Lucassifoni/hyperbolic-200mm-f3.5-/base mirror (ouch)/_MG_7760.JPG

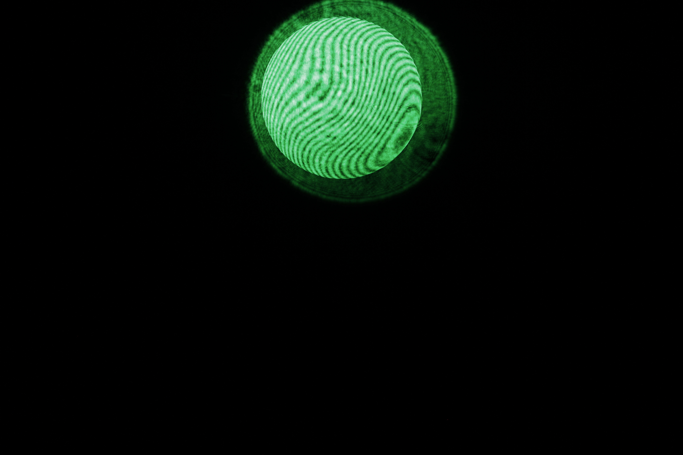
base mirror (ouch)/_MG_7760.JPG
