Lucassifoni/hyperbolic-200mm-f3.5-/base mirror (ouch)/Annotation 2022-02-02 160136.jpg

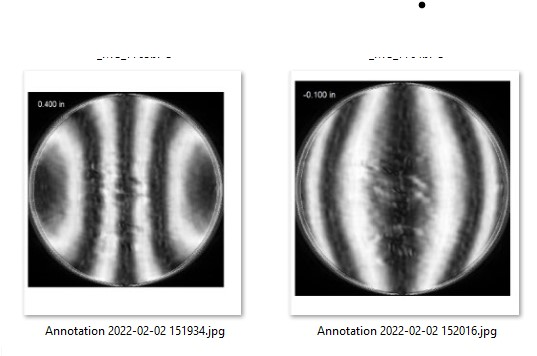
base mirror (ouch)/Annotation 2022-02-02 160136.jpg
