Lucassifoni/hyperbolic-200mm-f3.5-/base mirror (ouch)/fd45.jpg

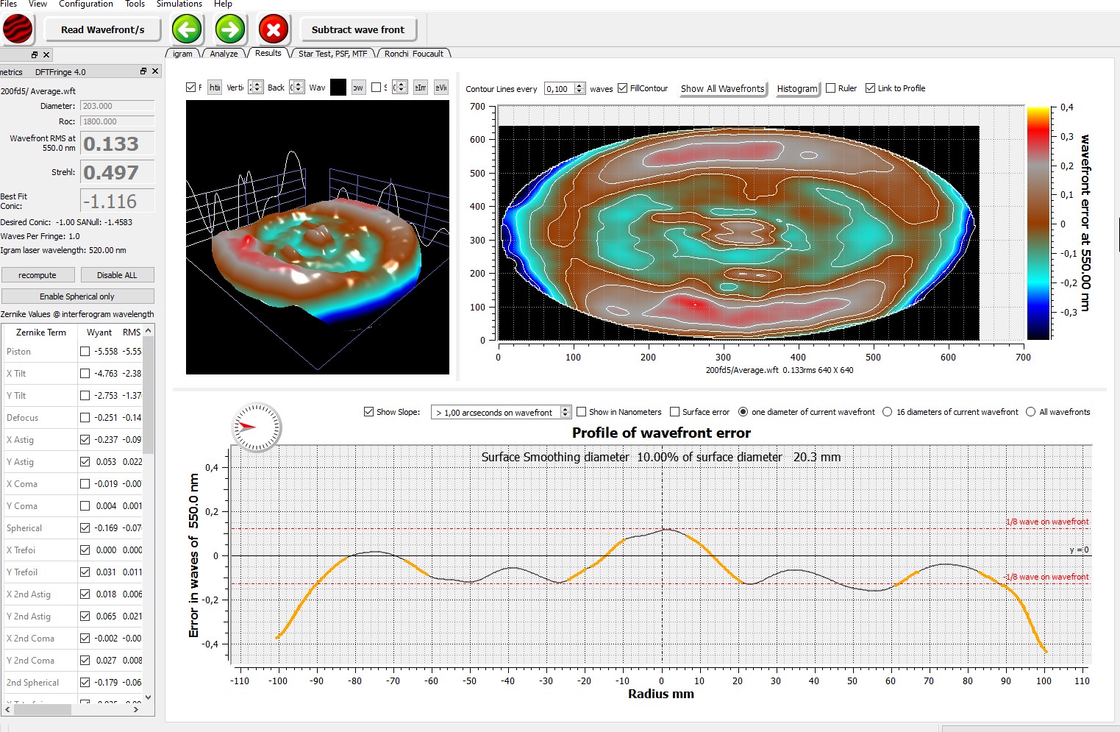
base mirror (ouch)/fd45.jpg
