Lucassifoni/hyperbolic-200mm-f3.5-/base mirror (ouch)/MPCC post-3008-0-78724300-1481155795.jpg

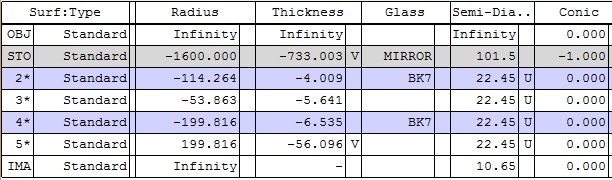
base mirror (ouch)/MPCC post-3008-0-78724300-1481155795.jpg
