Lucassifoni/hyperbolic-200mm-f3.5-/base mirror (ouch)/source/_MG_7740.JPG

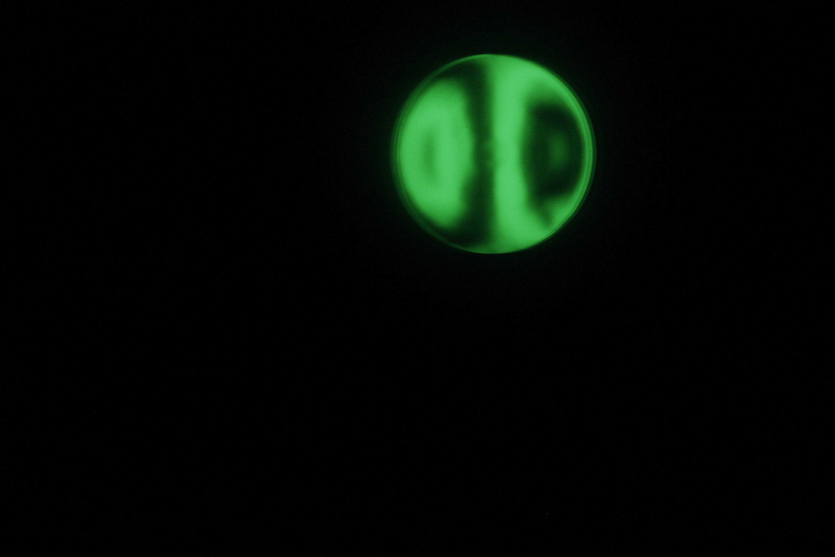
base mirror (ouch)/source/_MG_7740.JPG
