Lucassifoni/hyperbolic-200mm-f3.5-/base mirror (ouch)/source/_MG_7748.JPG

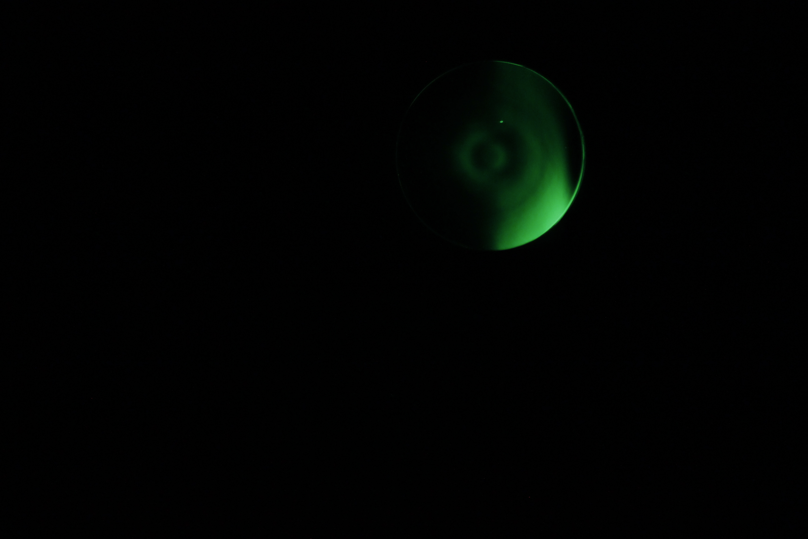
base mirror (ouch)/source/_MG_7748.JPG
