Lucassifoni/hyperbolic-200mm-f3.5-/figuring/session 0/0_sphere.jpeg

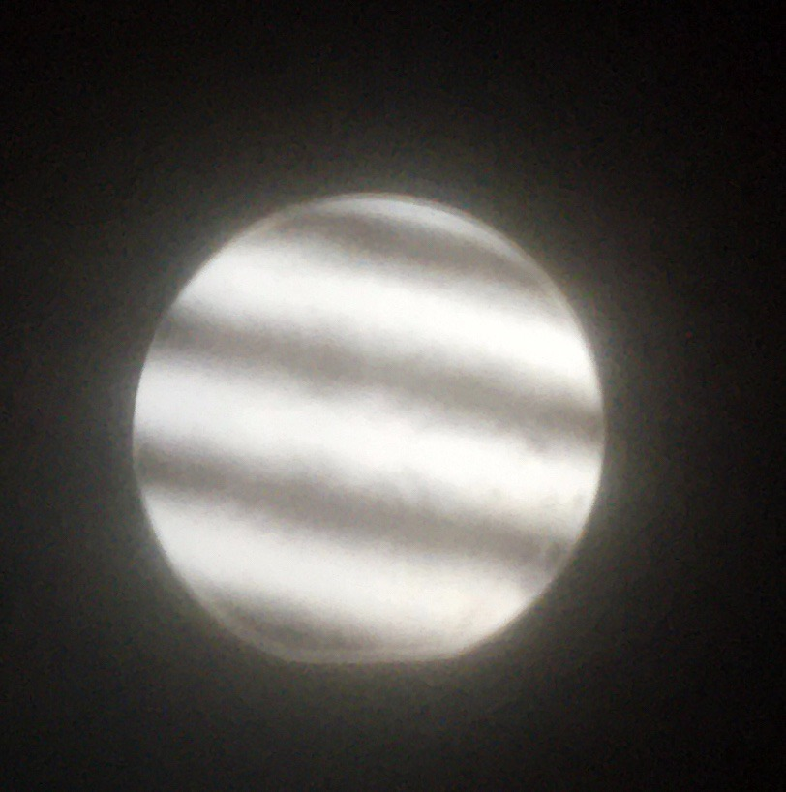
figuring/session 0/0_sphere.jpeg
