Lucassifoni/hyperbolic-200mm-f3.5-/figuring/session 1/1_outside.jpeg

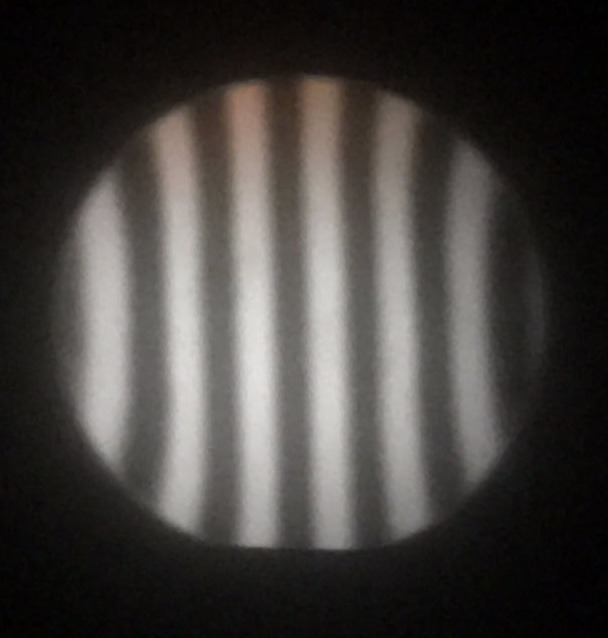
figuring/session 1/1_outside.jpeg
