Lucassifoni/hyperbolic-200mm-f3.5-/figuring/session 2/2_inside.jpeg

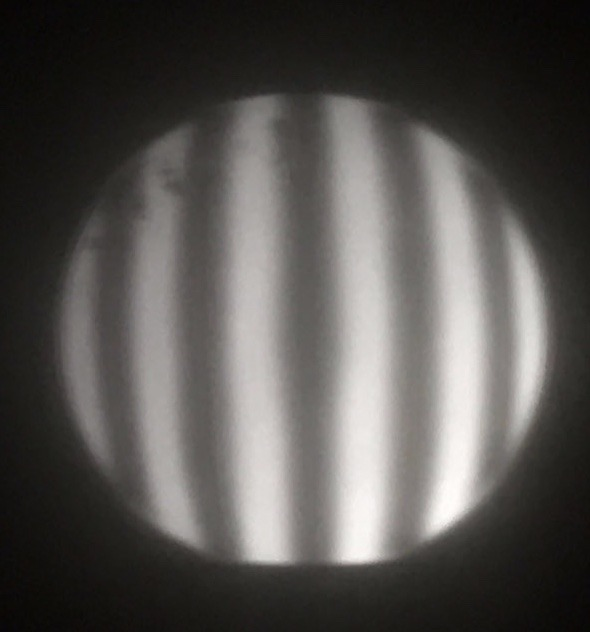
figuring/session 2/2_inside.jpeg
