Lucassifoni/hyperbolic-200mm-f3.5-/figuring/session 3/3_inside.jpeg

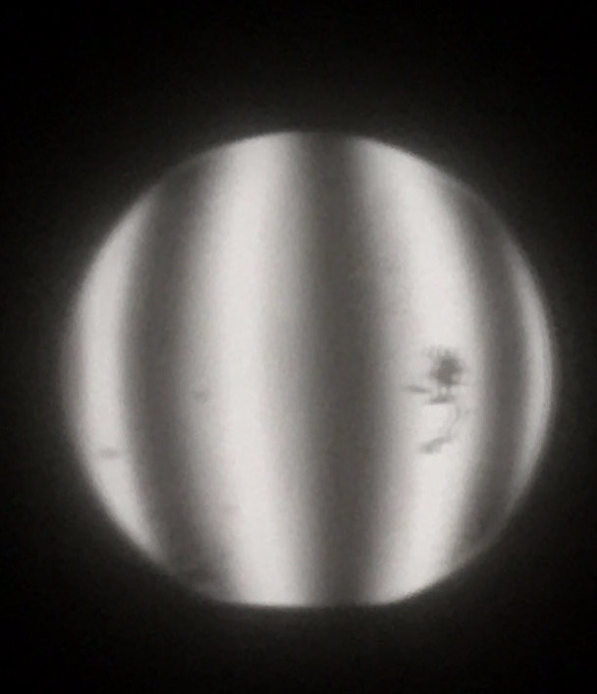
figuring/session 3/3_inside.jpeg
