Lucassifoni/hyperbolic-200mm-f3.5-/figuring/session 6/Capture.jpg

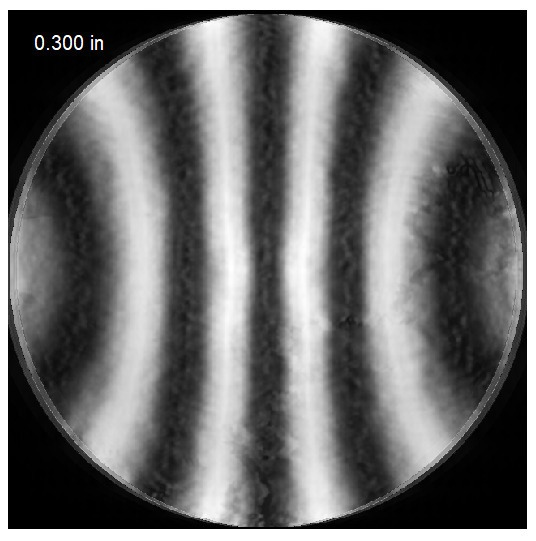
figuring/session 6/Capture.jpg
