Lucassifoni/hyperbolic-200mm-f3.5-/figuring/session 6/igrams/_MG_7814.JPG

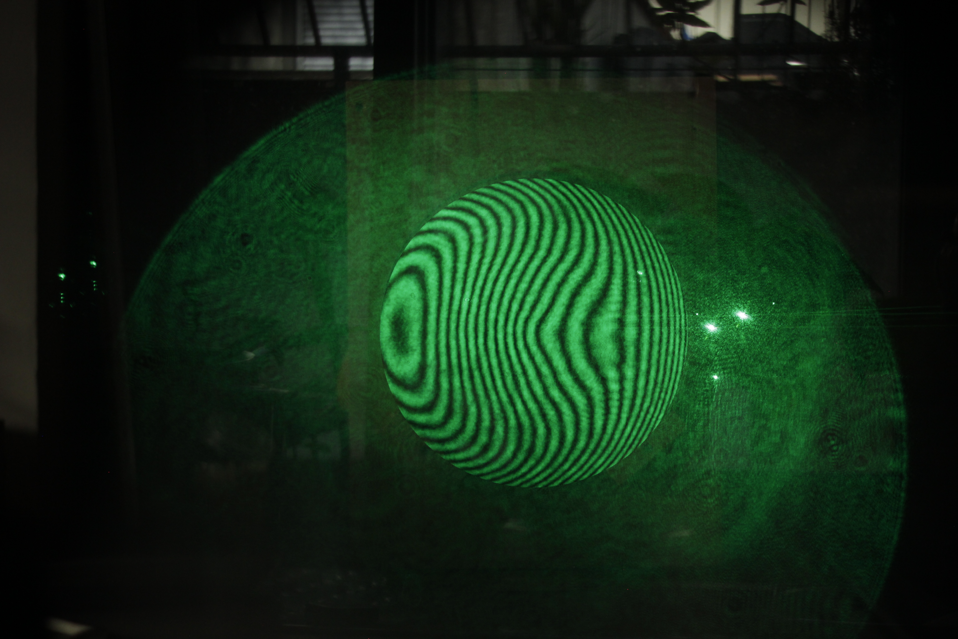
figuring/session 6/igrams/_MG_7814.JPG
