Lucassifoni/hyperbolic-200mm-f3.5-/figuring/session 7/lap.jpeg

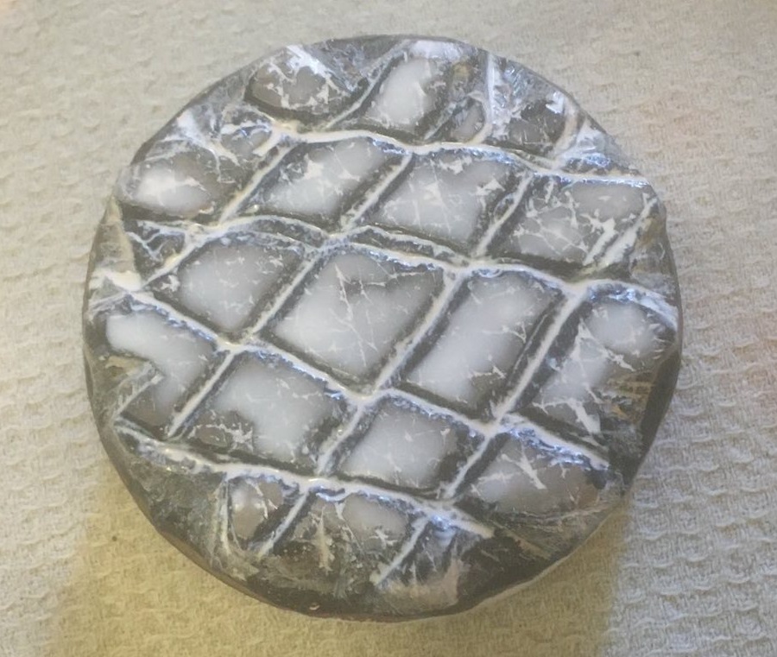
figuring/session 7/lap.jpeg
