Lucassifoni/hyperbolic-200mm-f3.5-/figuring/session 7/outside.jpeg

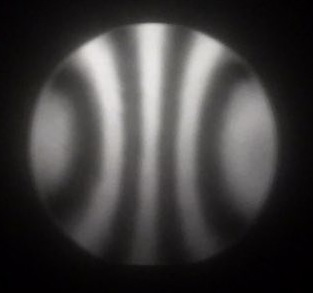
figuring/session 7/outside.jpeg
