Lucassifoni/hyperbolic-200mm-f3.5-/figuring/session 8/_MG_7846.JPG

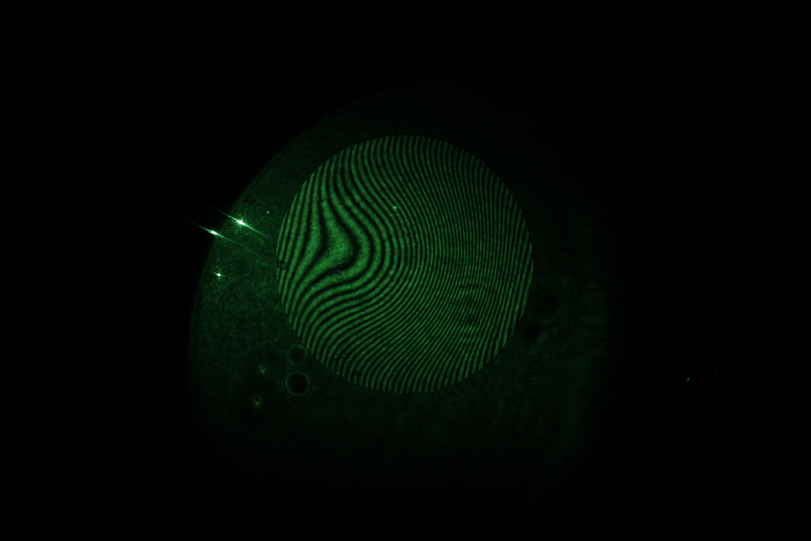
figuring/session 8/_MG_7846.JPG
