Lucassifoni/hyperbolic-200mm-f3.5-/figuring/session 8/_MG_7848.JPG

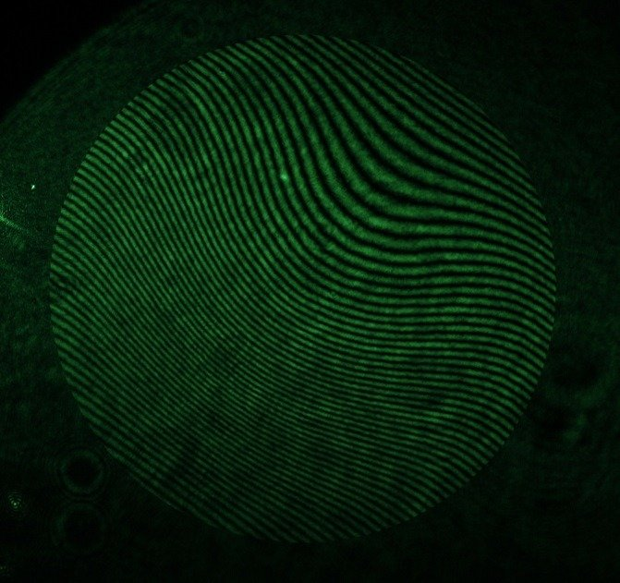
figuring/session 8/_MG_7848.JPG
