Lucassifoni/hyperbolic-200mm-f3.5-/figuring/session 8/Capture.JPG

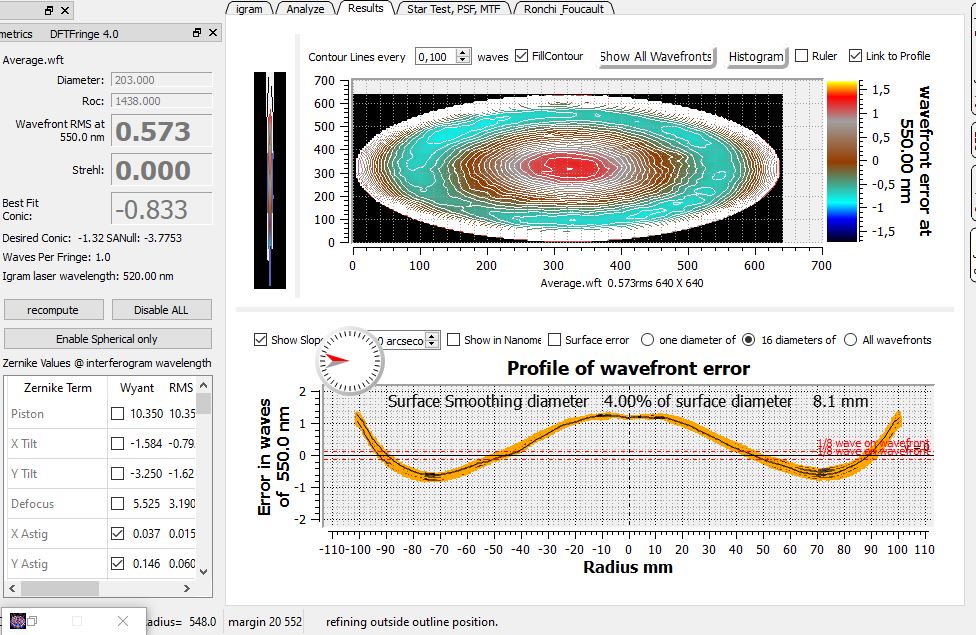
figuring/session 8/Capture.JPG
