Lucassifoni/hyperbolic-200mm-f3.5-/figuring/session 9/_MG_7857.JPG

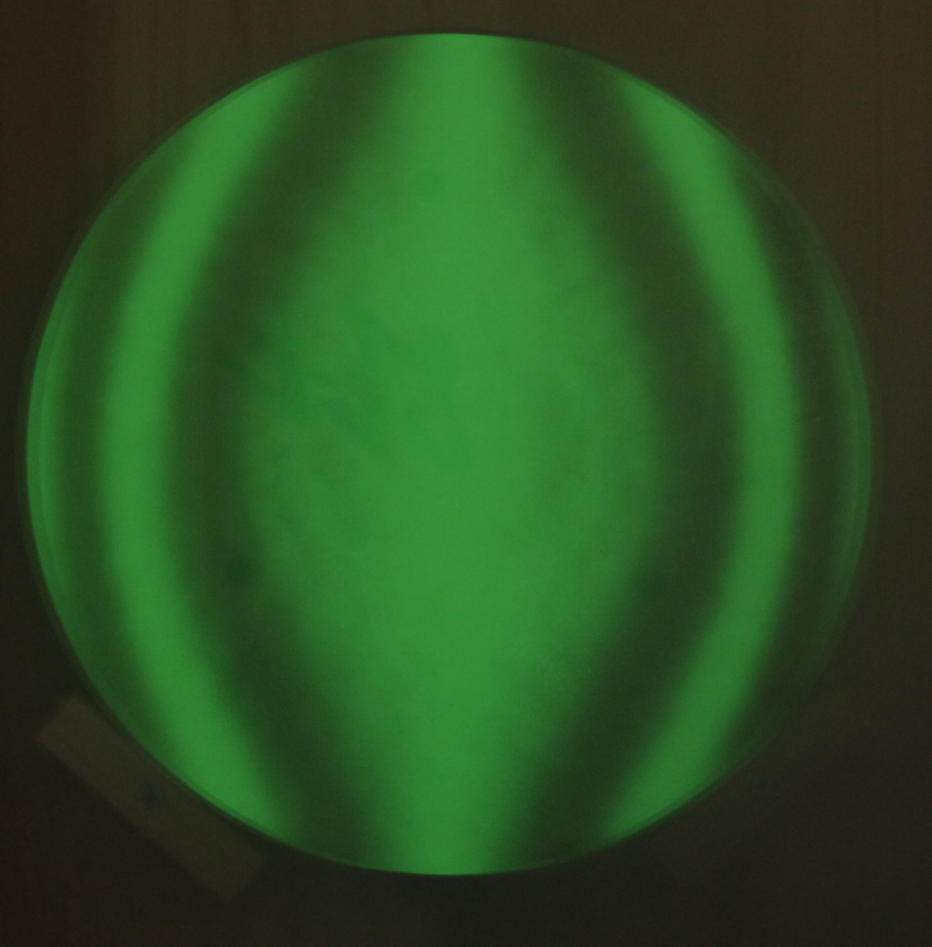
figuring/session 9/_MG_7857.JPG
