Lucassifoni/hyperbolic-200mm-f3.5-/figuring/session 11/_MG_7869.JPG

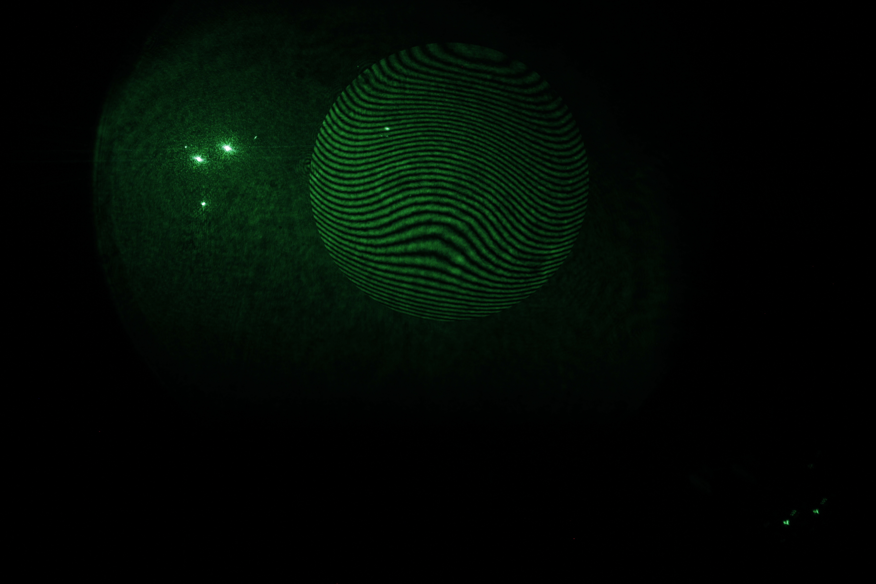
figuring/session 11/_MG_7869.JPG
