Lucassifoni/hyperbolic-200mm-f3.5-/figuring/session 11/_MG_7881.JPG

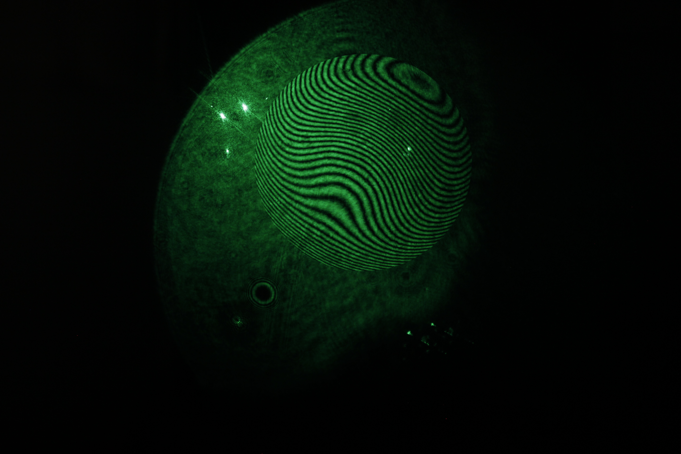
figuring/session 11/_MG_7881.JPG
