Lucassifoni/hyperbolic-200mm-f3.5-/figuring/session 12/_MG_7891.JPG

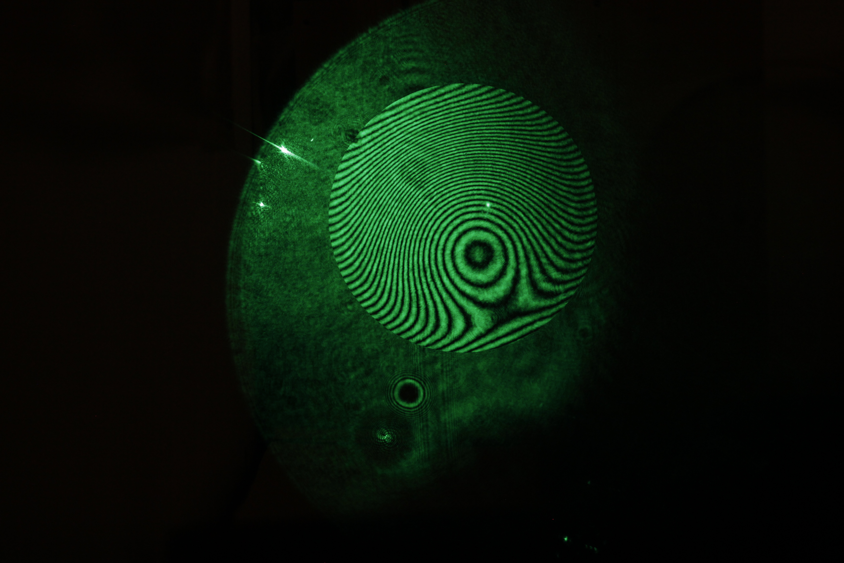
figuring/session 12/_MG_7891.JPG
