Lucassifoni/hyperbolic-200mm-f3.5-/figuring/session 12/_MG_7892.JPG

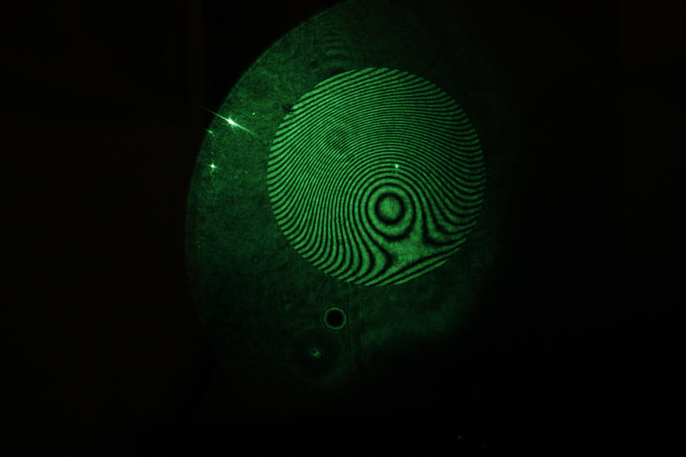
figuring/session 12/_MG_7892.JPG
