Lucassifoni/hyperbolic-200mm-f3.5-/figuring/session 12/Capture.JPG

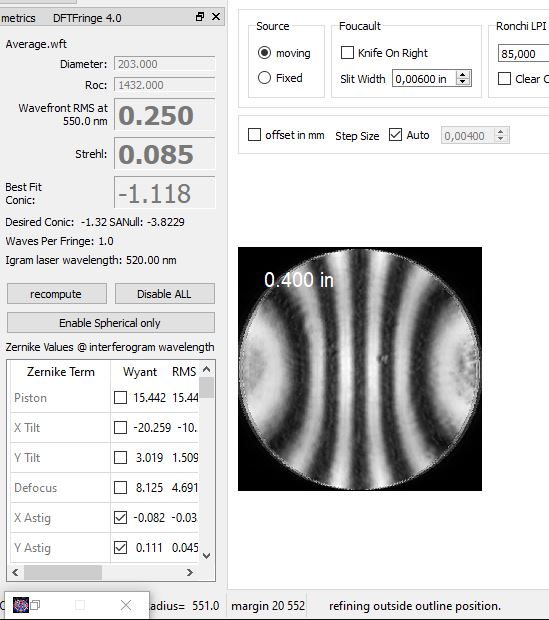
figuring/session 12/Capture.JPG
