Lucassifoni/hyperbolic-200mm-f3.5-/figuring/session 14/_MG_7916.JPG

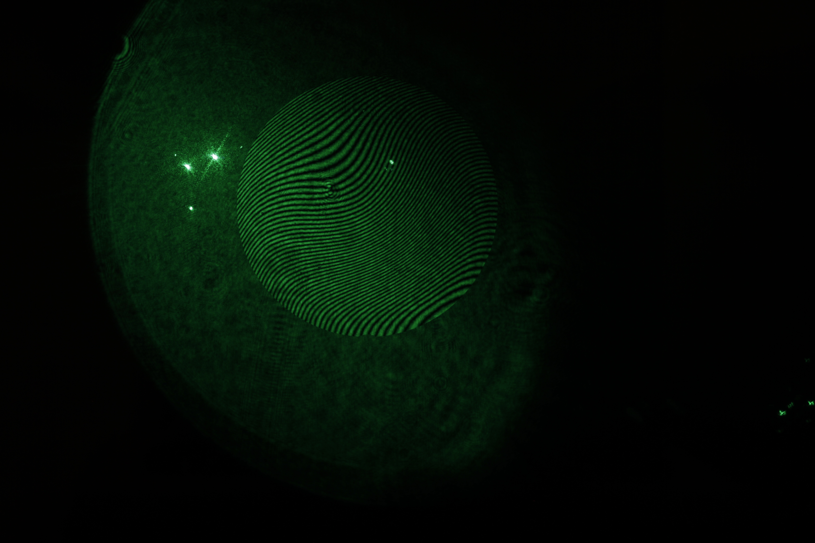
figuring/session 14/_MG_7916.JPG
