Lucassifoni/hyperbolic-200mm-f3.5-/figuring/session 14/_MG_7924.JPG

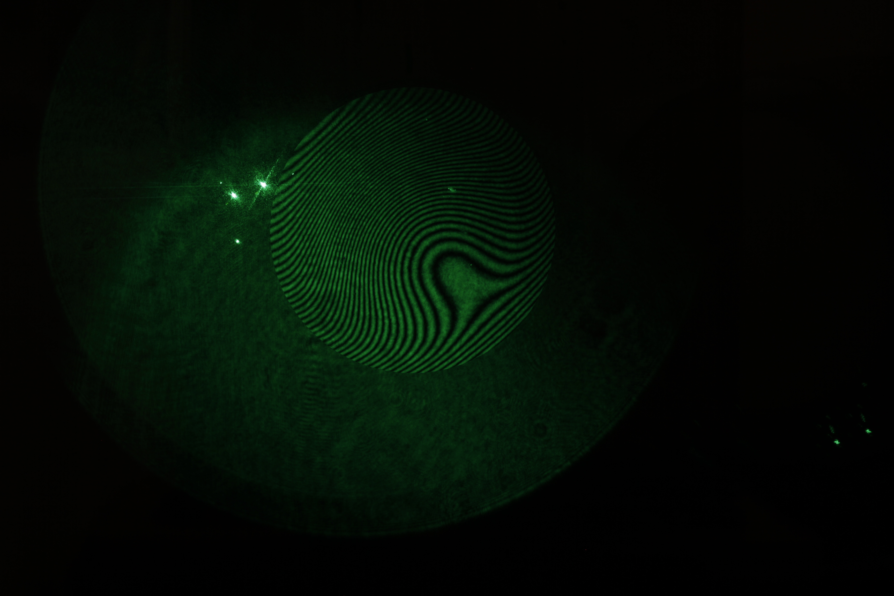
figuring/session 14/_MG_7924.JPG
