Lucassifoni/hyperbolic-200mm-f3.5-/figuring/session 14/Capture.JPG

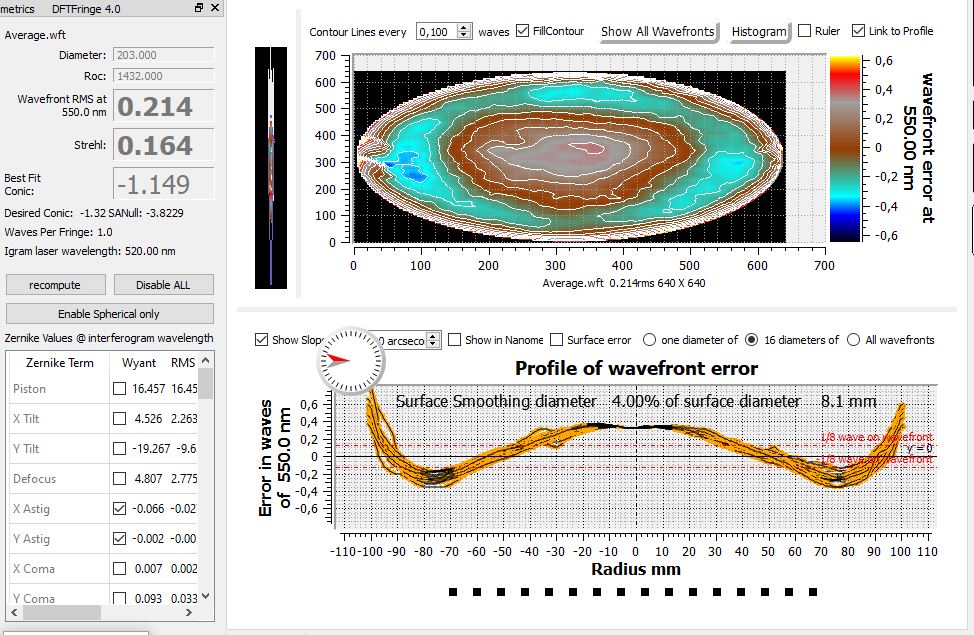
figuring/session 14/Capture.JPG
