Lucassifoni/hyperbolic-200mm-f3.5-/figuring/session 15/_MG_7925.JPG

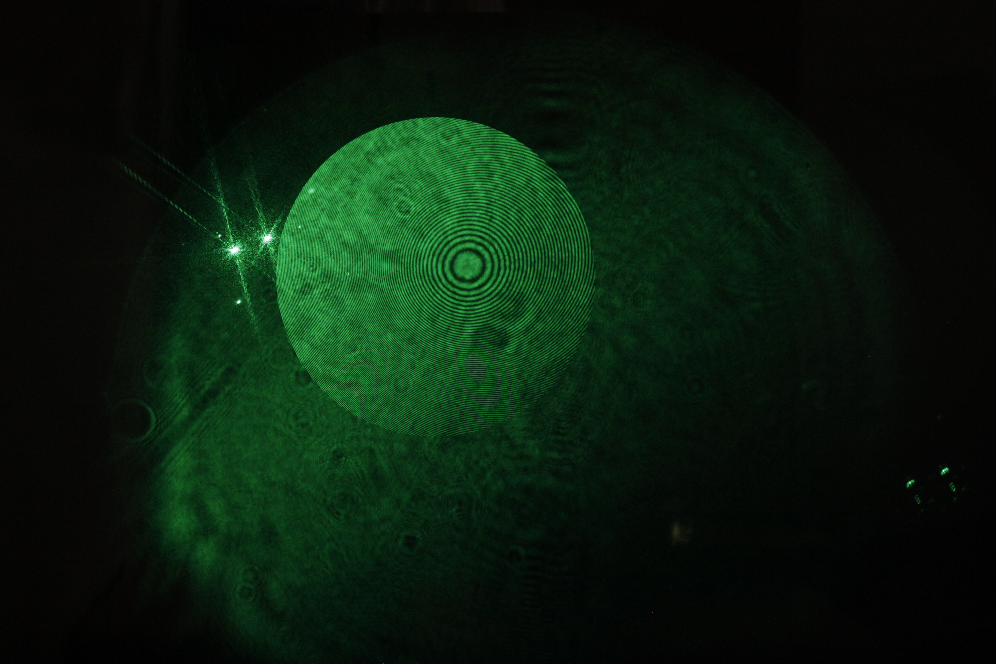
figuring/session 15/_MG_7925.JPG
