Lucassifoni/hyperbolic-200mm-f3.5-/figuring/session 15/_MG_7926.JPG

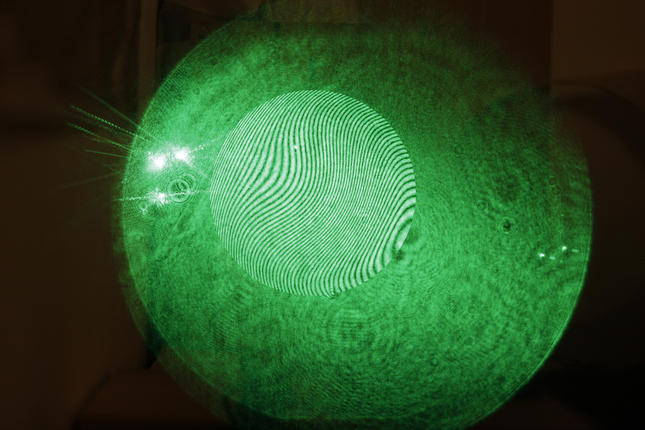
figuring/session 15/_MG_7926.JPG
