Lucassifoni/hyperbolic-200mm-f3.5-/figuring/session 15/Capture.JPG

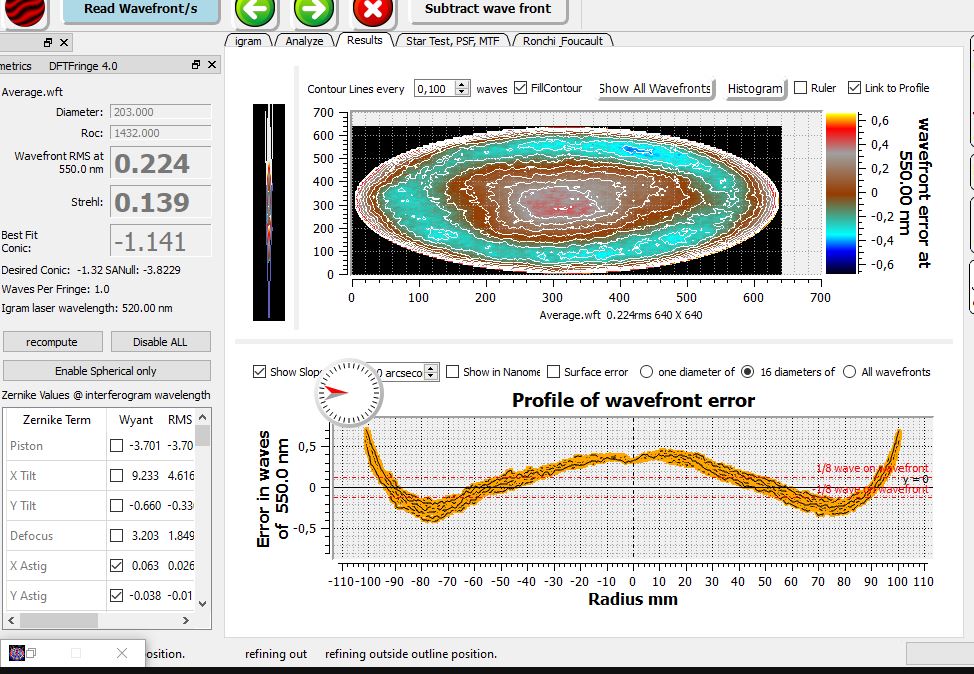
figuring/session 15/Capture.JPG
