Lucassifoni/hyperbolic-200mm-f3.5-/figuring/session 16/_MG_7944.JPG

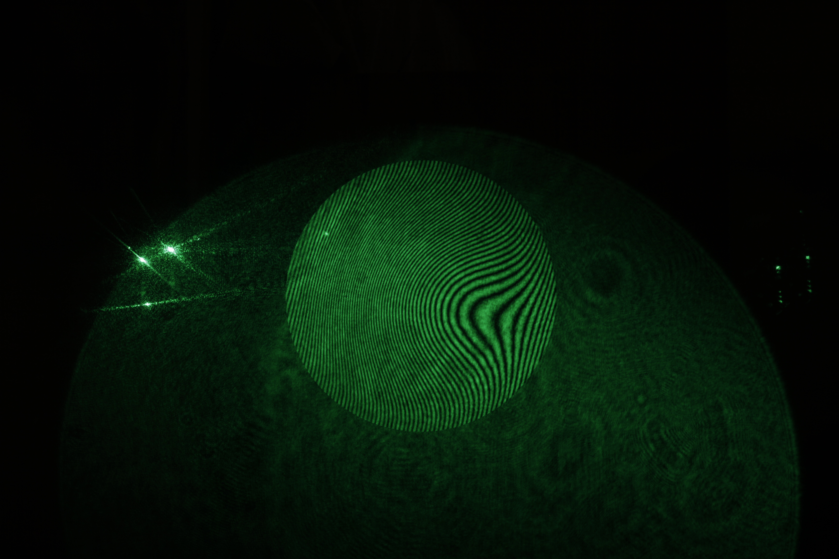
figuring/session 16/_MG_7944.JPG
