Lucassifoni/hyperbolic-200mm-f3.5-/figuring/session 16/unknown.png

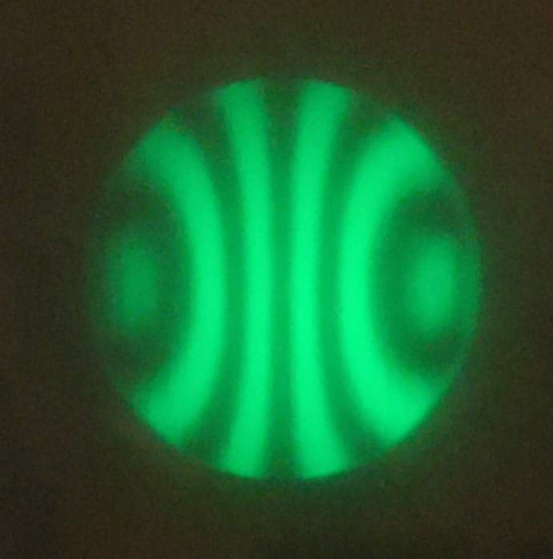
figuring/session 16/unknown.png
