Lucassifoni/hyperbolic-200mm-f3.5-/figuring/session 17/_MG_7948.JPG

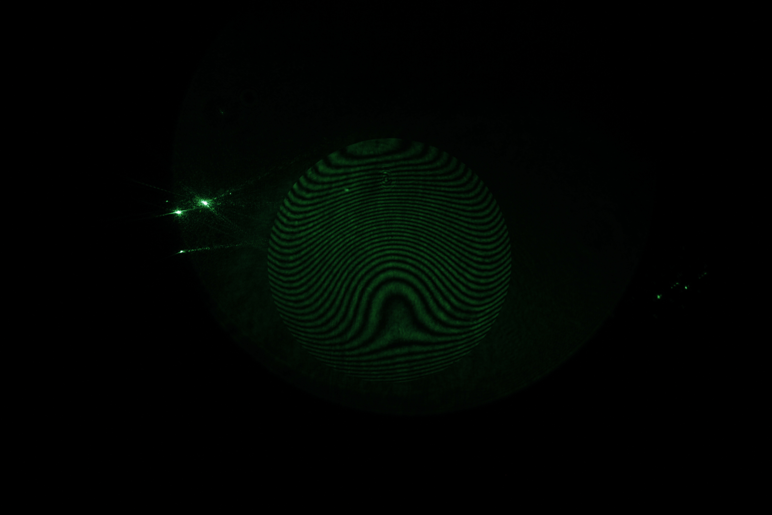
figuring/session 17/_MG_7948.JPG
