Lucassifoni/hyperbolic-200mm-f3.5-/figuring/session 17/CaptureSession17.PNG

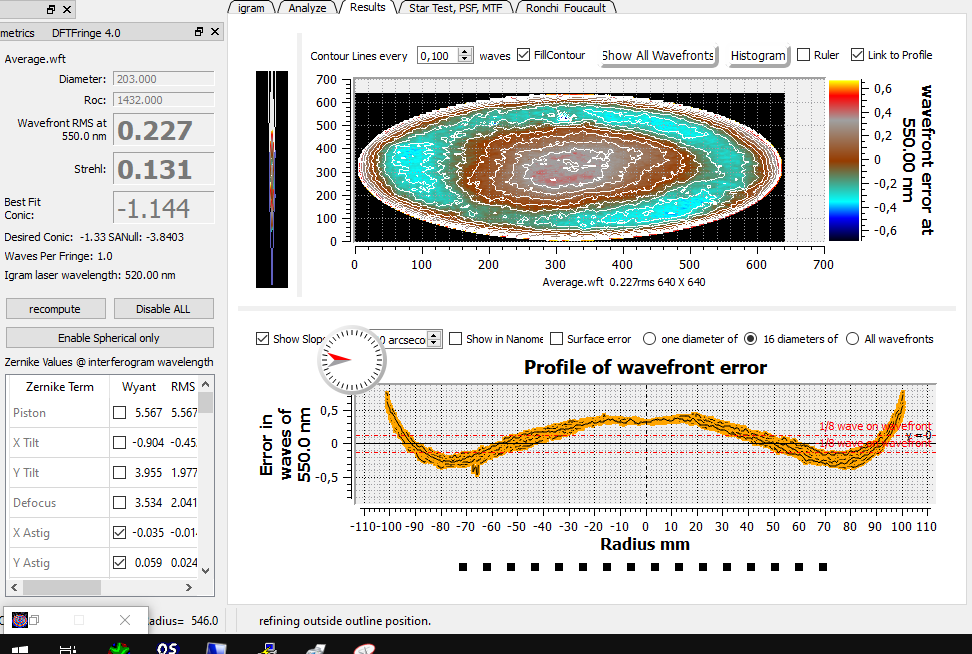
figuring/session 17/CaptureSession17.PNG
