Lucassifoni/hyperbolic-200mm-f3.5-/figuring/session 18/_MG_7953.JPG

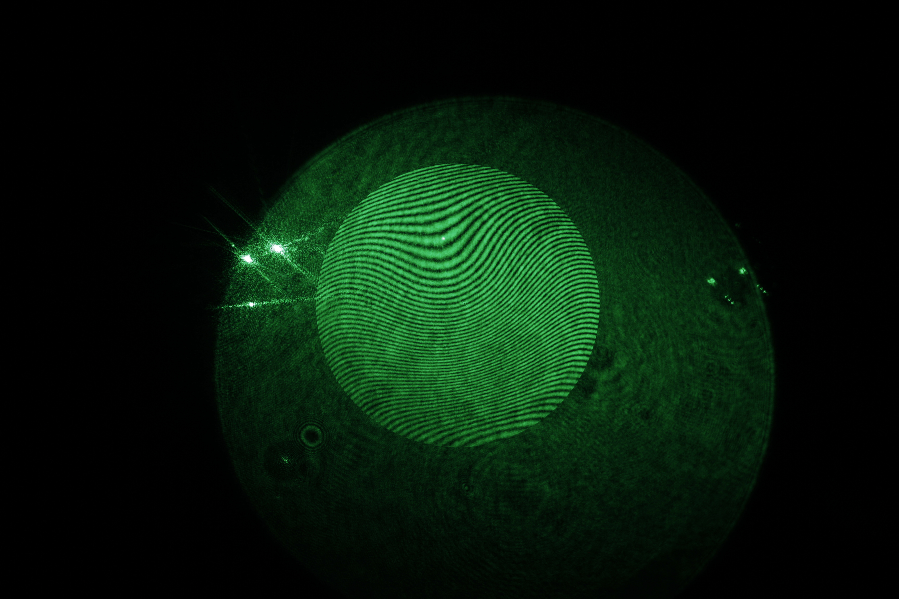
figuring/session 18/_MG_7953.JPG
