Lucassifoni/hyperbolic-200mm-f3.5-/figuring/session 18/Capture.PNG

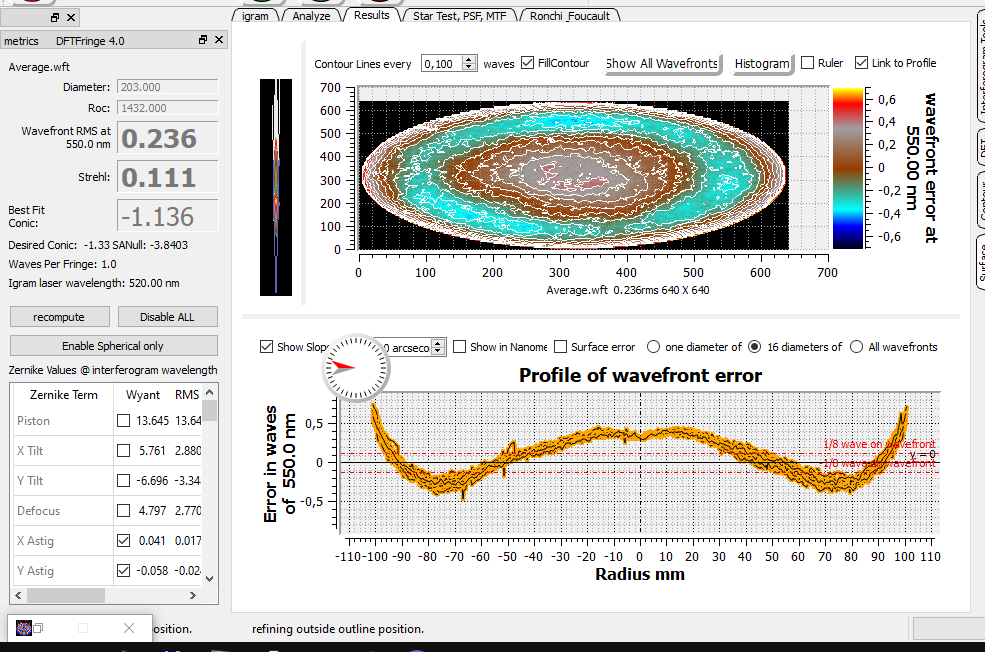
figuring/session 18/Capture.PNG
