Lucassifoni/hyperbolic-200mm-f3.5-/figuring/session 20/_MG_7962.JPG

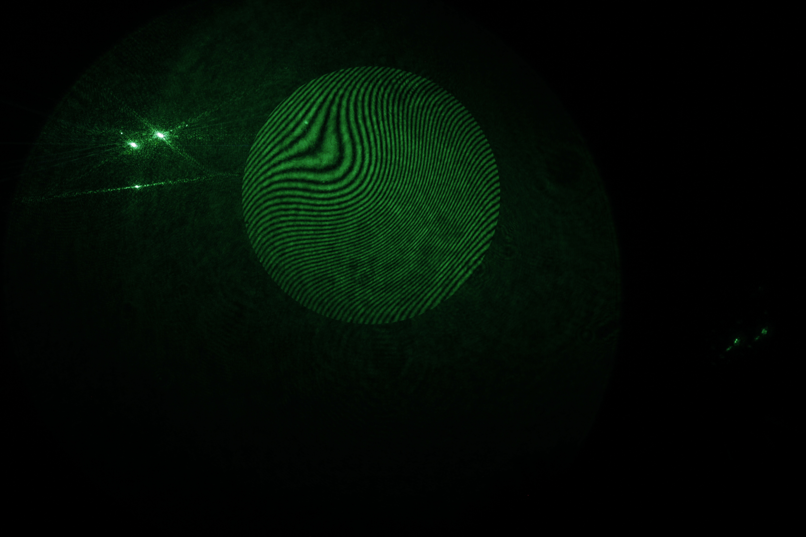
figuring/session 20/_MG_7962.JPG
