Lucassifoni/hyperbolic-200mm-f3.5-/figuring/session 21/m1/_MG_7965.JPG

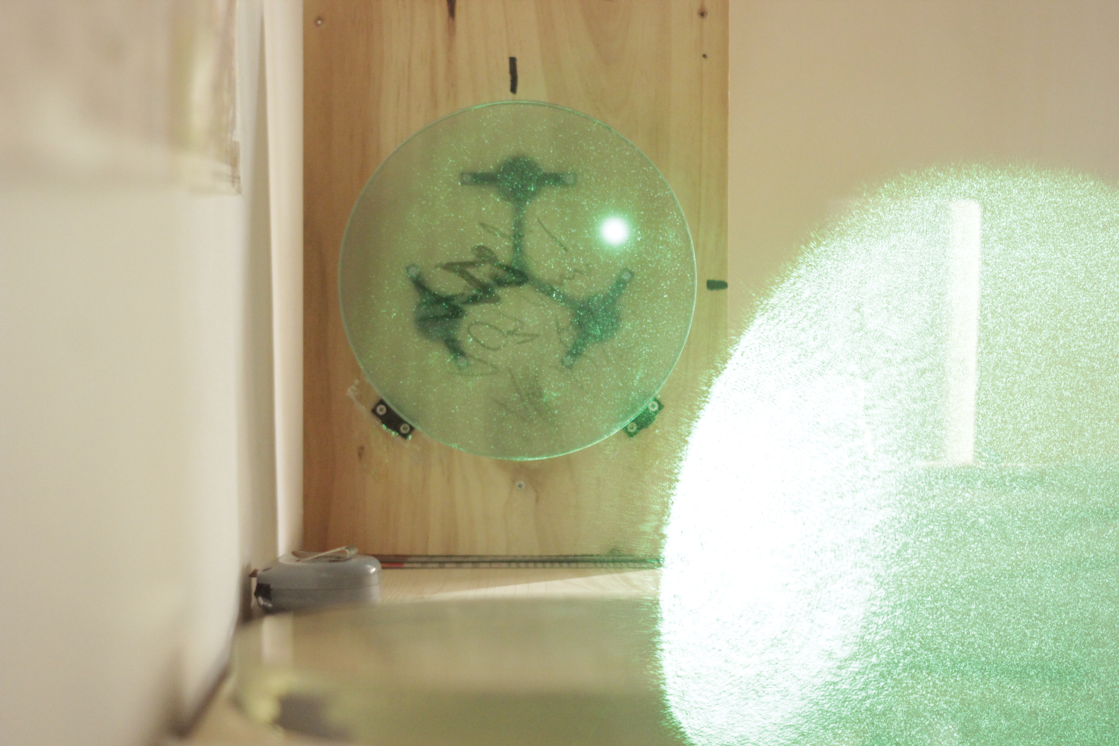
figuring/session 21/m1/_MG_7965.JPG
