Lucassifoni/hyperbolic-200mm-f3.5-/figuring/session 21/m2/_MG_7981.JPG

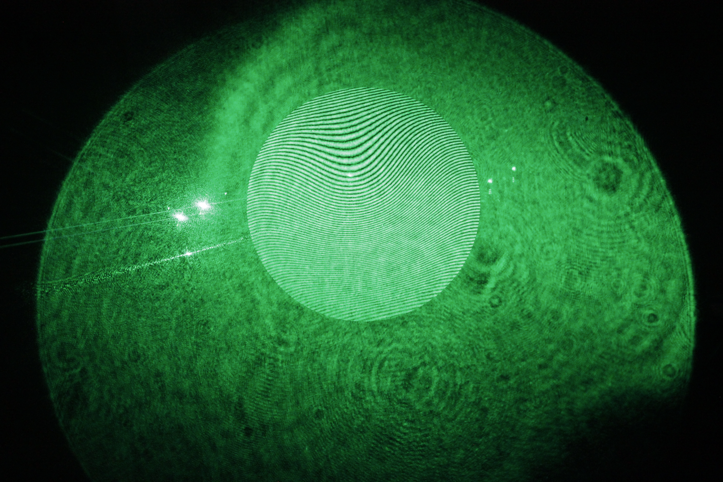
figuring/session 21/m2/_MG_7981.JPG
