Lucassifoni/hyperbolic-200mm-f3.5-/figuring/session 22/_MG_7995.JPG

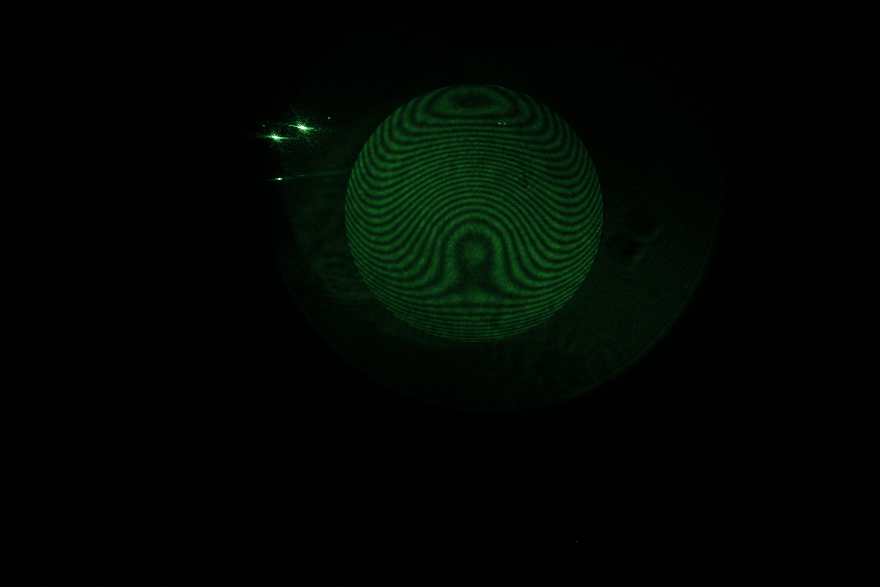
figuring/session 22/_MG_7995.JPG
