Lucassifoni/hyperbolic-200mm-f3.5-/figuring/session 23/_MG_8008.JPG

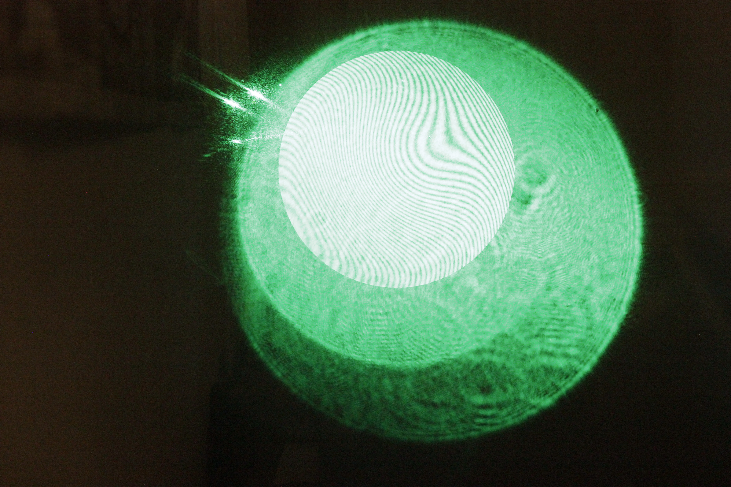
figuring/session 23/_MG_8008.JPG
