Lucassifoni/hyperbolic-200mm-f3.5-/figuring/session 23/Capture.PNG

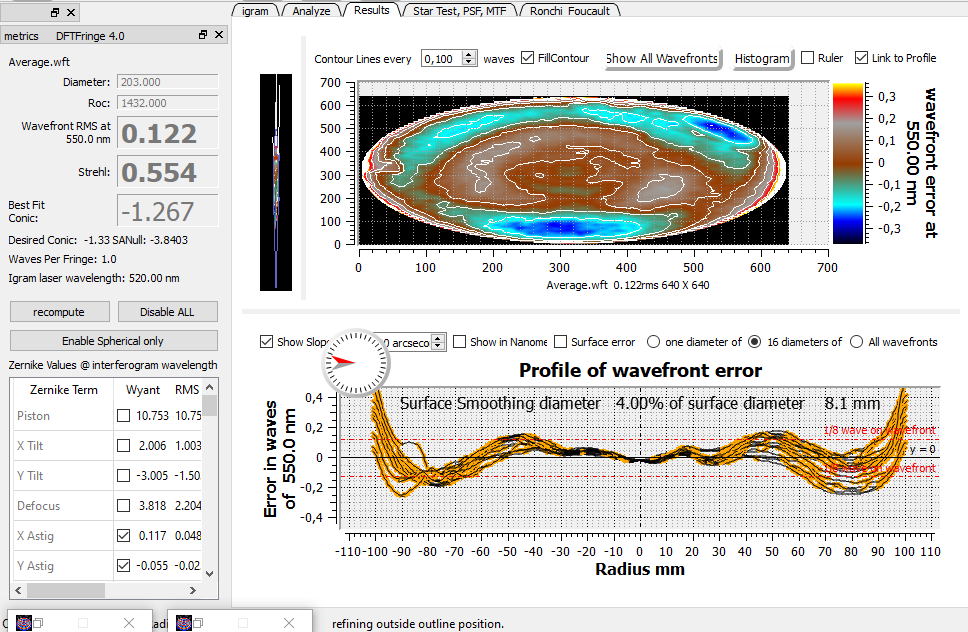
figuring/session 23/Capture.PNG
