Lucassifoni/hyperbolic-200mm-f3.5-/figuring/session 25/_MG_8024.JPG

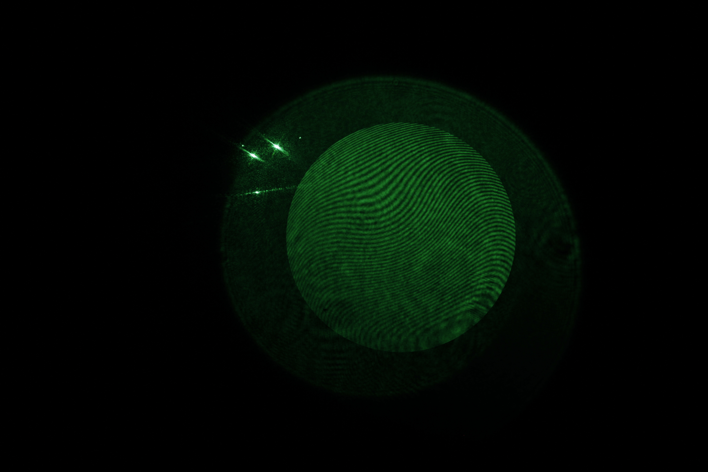
figuring/session 25/_MG_8024.JPG
