Lucassifoni/hyperbolic-200mm-f3.5-/figuring/session 26/a1/_MG_8036.JPG

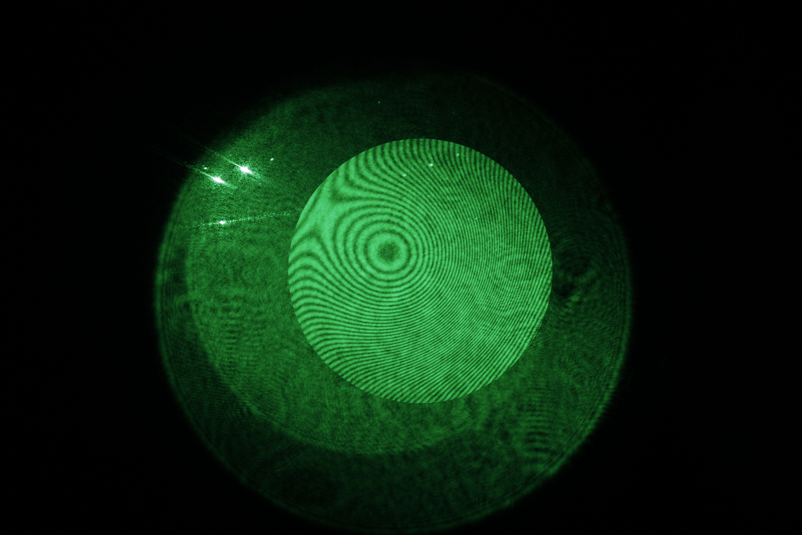
figuring/session 26/a1/_MG_8036.JPG
