Lucassifoni/hyperbolic-200mm-f3.5-/figuring/session 26/a2/_MG_8045.JPG

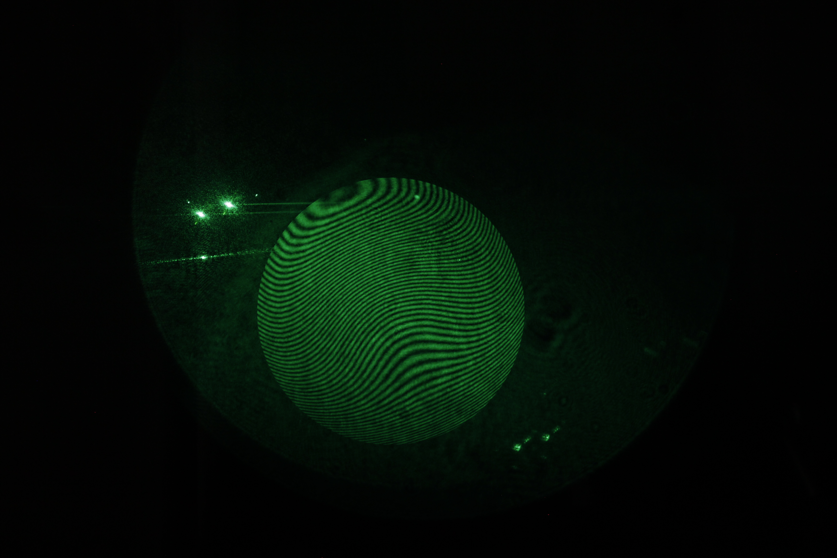
figuring/session 26/a2/_MG_8045.JPG
