Lucassifoni/hyperbolic-200mm-f3.5-/figuring/session 27/_MG_8078.JPG

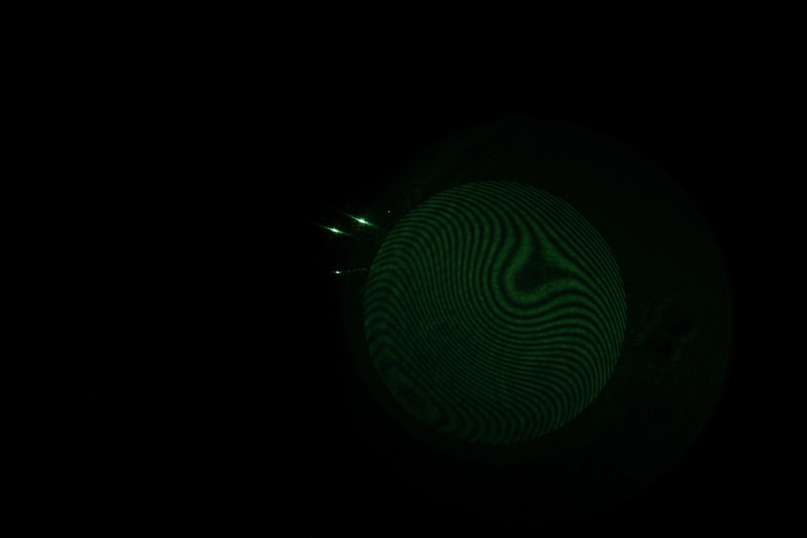
figuring/session 27/_MG_8078.JPG
