Lucassifoni/hyperbolic-200mm-f3.5-/figuring/session 27/Capture.PNG

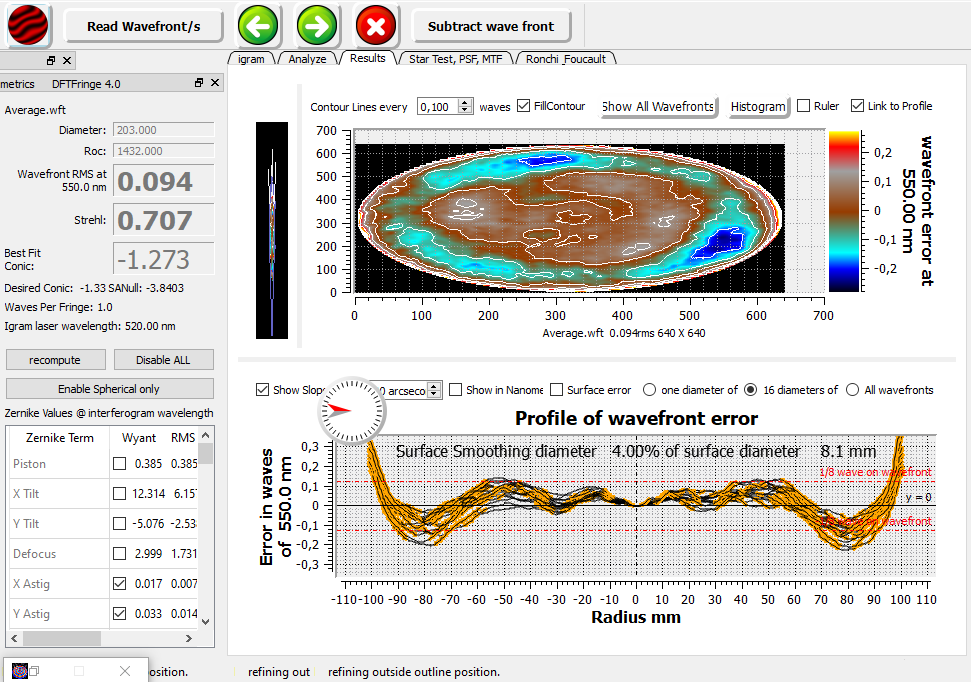
figuring/session 27/Capture.PNG
