Lucassifoni/hyperbolic-200mm-f3.5-/figuring/session 29/_MG_8104.JPG

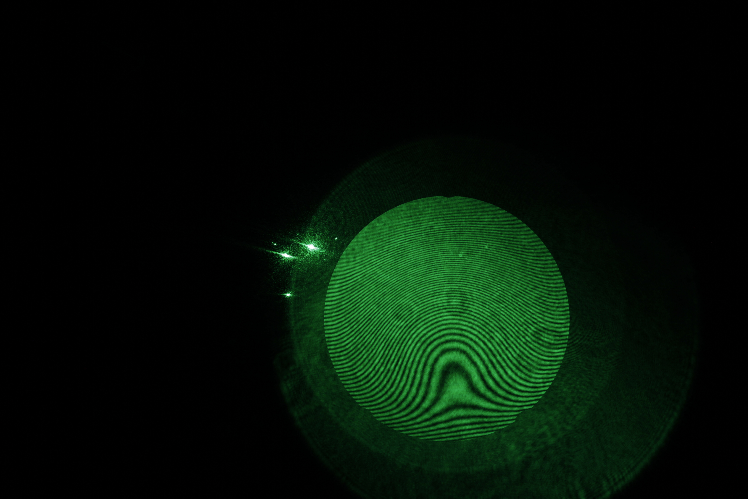
figuring/session 29/_MG_8104.JPG
