Lucassifoni/hyperbolic-200mm-f3.5-/figuring/session 31 - smoothing/_MG_8124.JPG

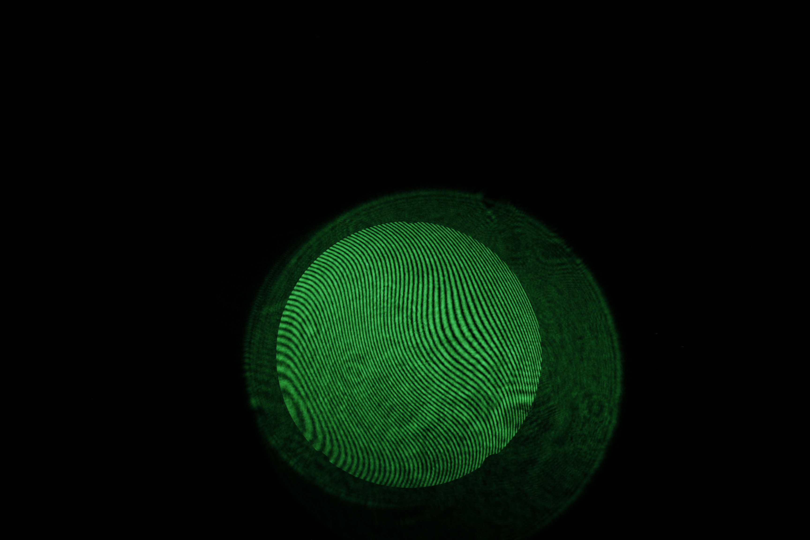
figuring/session 31 - smoothing/_MG_8124.JPG
