Lucassifoni/hyperbolic-200mm-f3.5-/figuring/session 32/_MG_8141.JPG

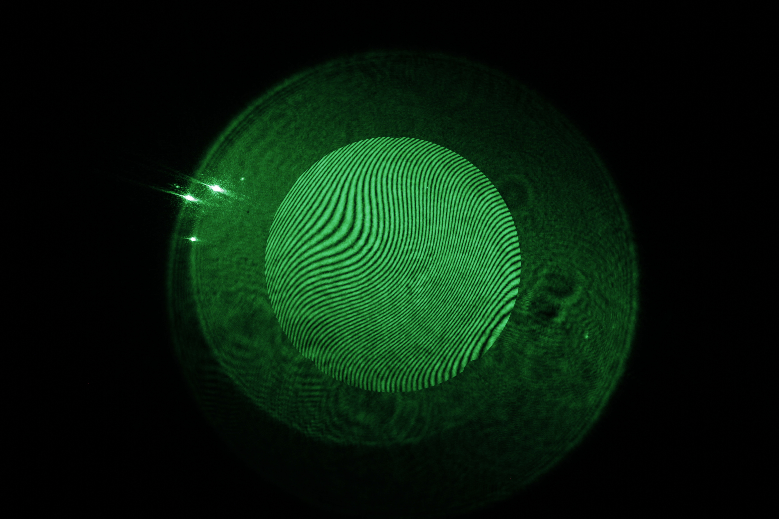
figuring/session 32/_MG_8141.JPG
