Lucassifoni/hyperbolic-200mm-f3.5-/figuring/session 33/_MG_8156.JPG

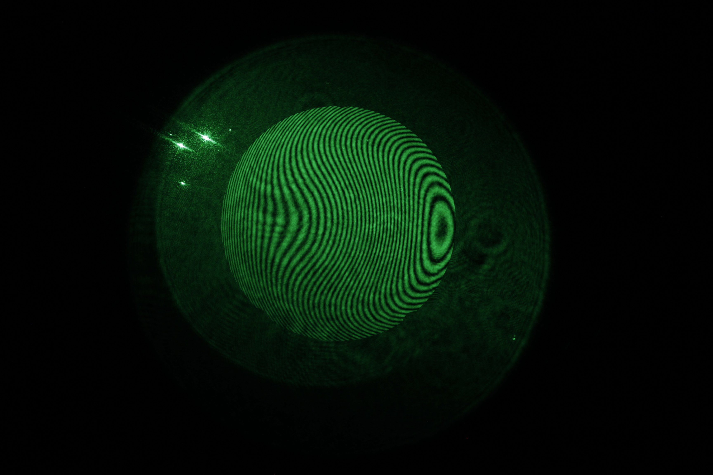
figuring/session 33/_MG_8156.JPG
