Lucassifoni/hyperbolic-200mm-f3.5-/figuring/session 34/_MG_8167.JPG

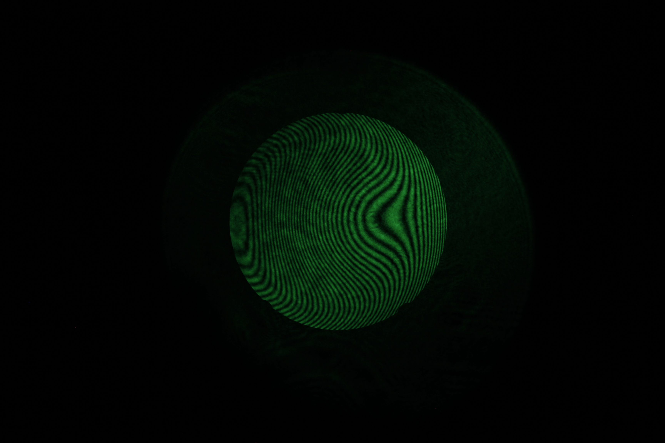
figuring/session 34/_MG_8167.JPG
