Lucassifoni/hyperbolic-200mm-f3.5-/figuring/session 34/_MG_8175.JPG

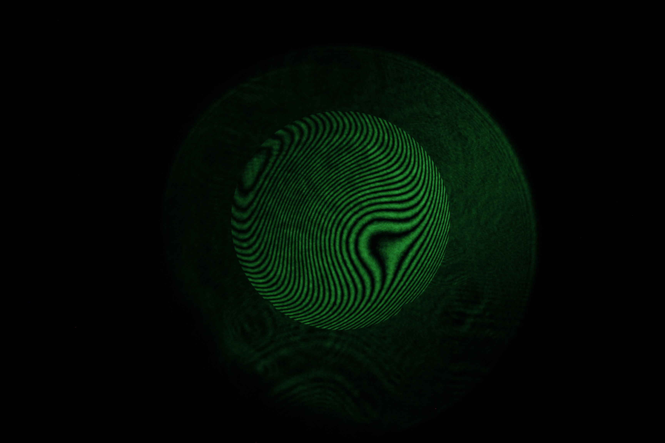
figuring/session 34/_MG_8175.JPG
