Lucassifoni/hyperbolic-200mm-f3.5-/figuring/session 34/avg.JPG

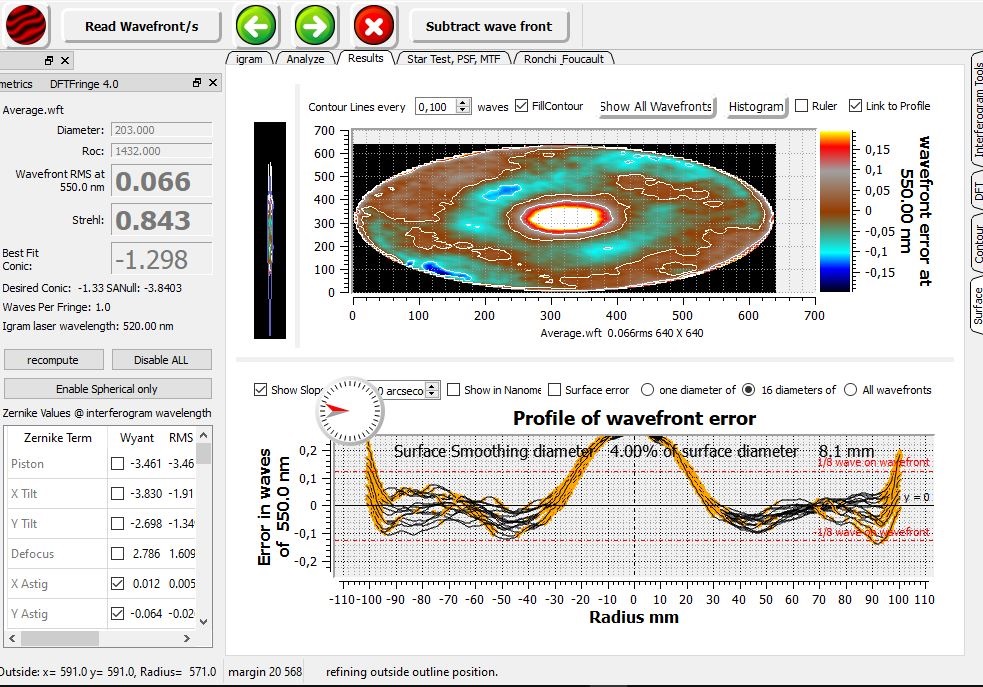
figuring/session 34/avg.JPG
