Lucassifoni/hyperbolic-200mm-f3.5-/figuring/session 34/dia1.JPG

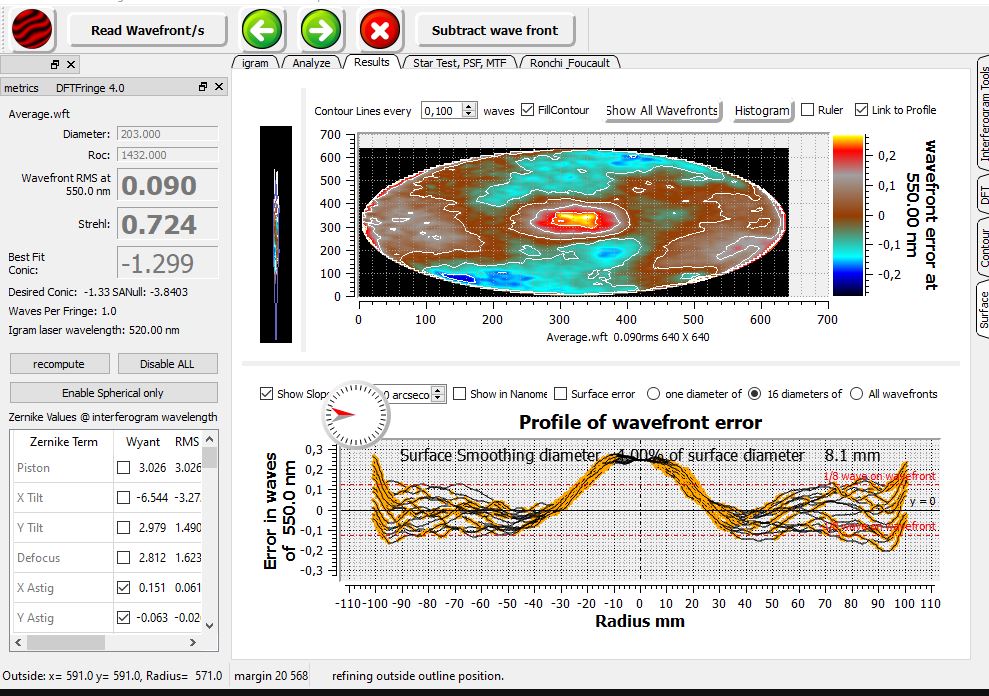
figuring/session 34/dia1.JPG
