Lucassifoni/hyperbolic-200mm-f3.5-/figuring/session 34/signal-2022-04-09-172335_001.png

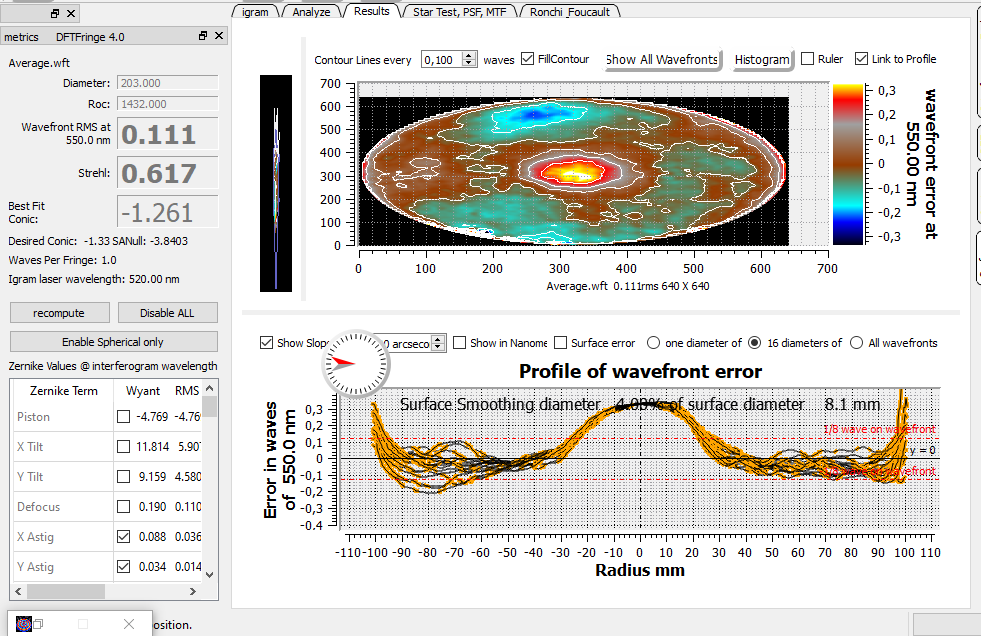
figuring/session 34/signal-2022-04-09-172335_001.png
