Lucassifoni/hyperbolic-200mm-f3.5-/figuring/session 38/_MG_8240.JPG

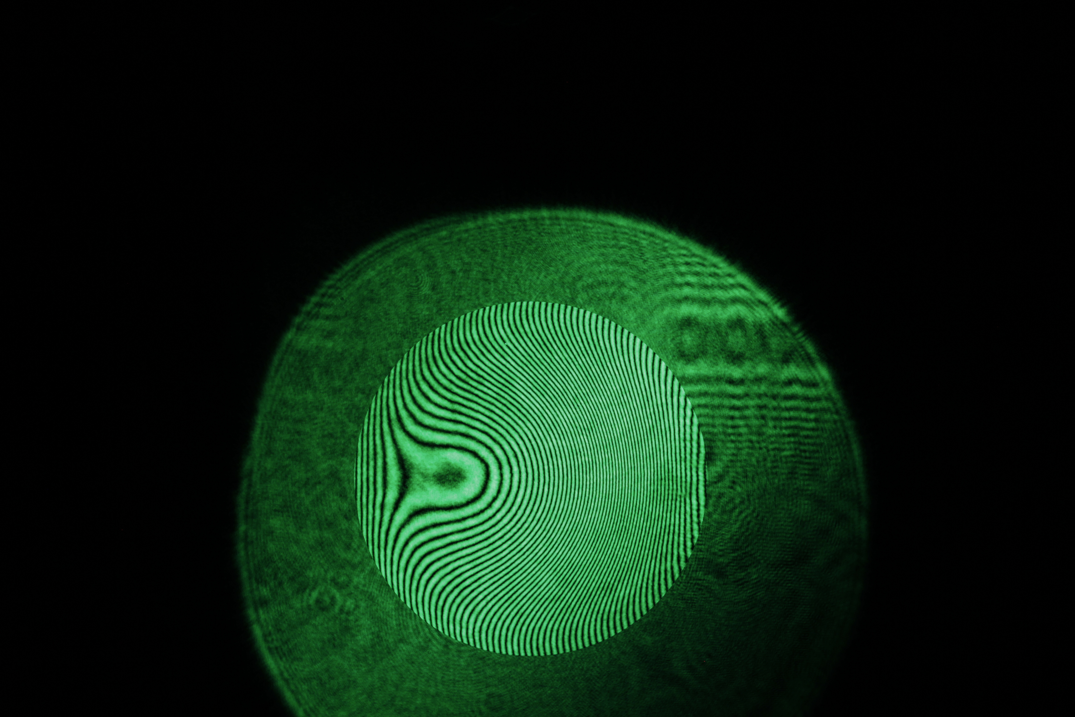
figuring/session 38/_MG_8240.JPG
