Lucassifoni/hyperbolic-200mm-f3.5-/figuring/session 38/_MG_8241.JPG

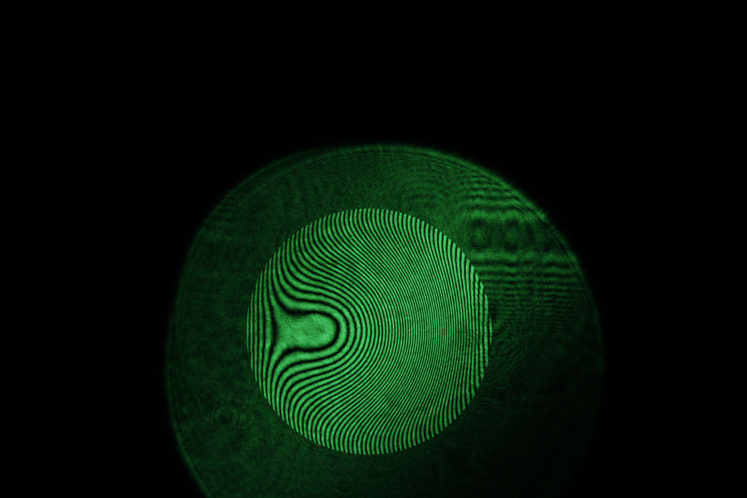
figuring/session 38/_MG_8241.JPG
