Lucassifoni/hyperbolic-200mm-f3.5-/figuring/session 39/_MG_8265.JPG

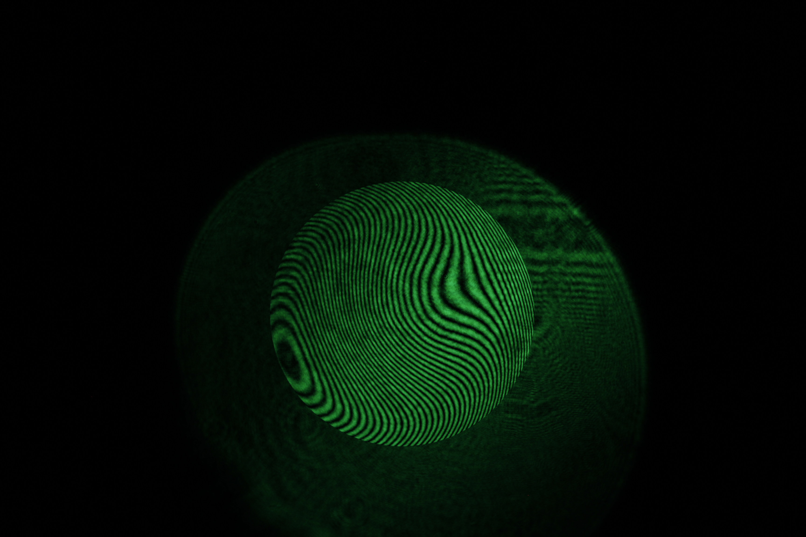
figuring/session 39/_MG_8265.JPG
