Lucassifoni/hyperbolic-200mm-f3.5-/figuring/session 40/_MG_8280.JPG

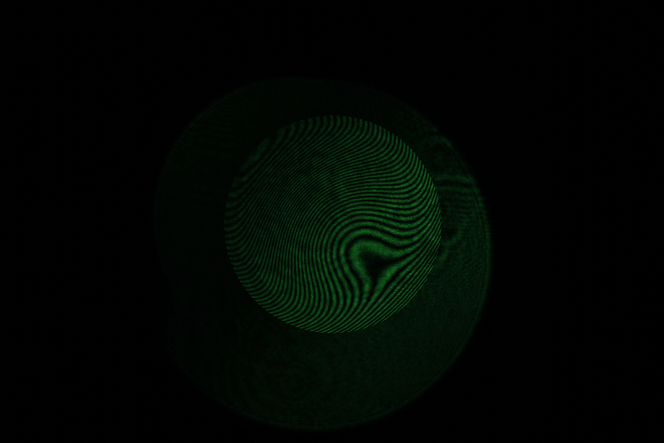
figuring/session 40/_MG_8280.JPG
