Lucassifoni/hyperbolic-200mm-f3.5-/figuring/session 41/r0/_MG_8286.JPG

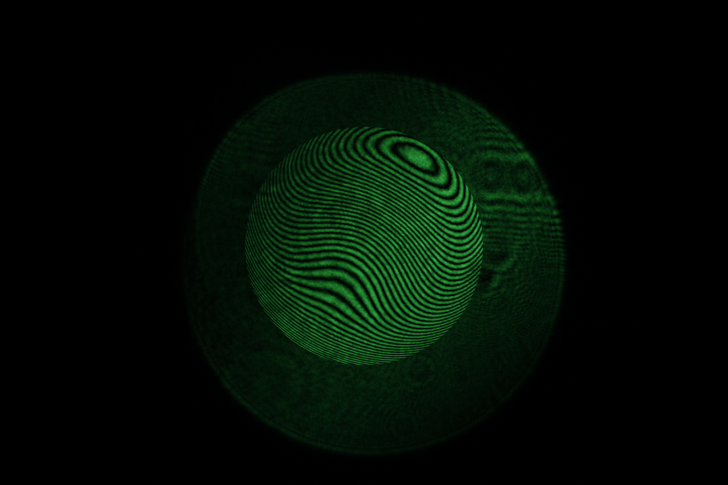
figuring/session 41/r0/_MG_8286.JPG
