Lucassifoni/hyperbolic-200mm-f3.5-/figuring/session 42/_MG_8332.JPG

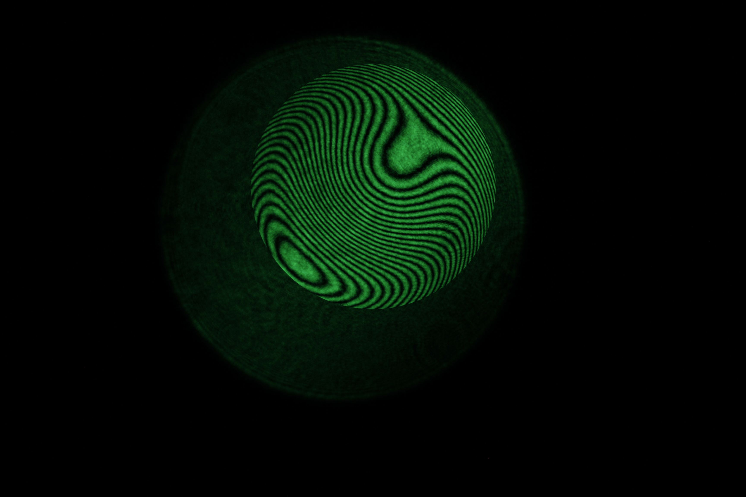
figuring/session 42/_MG_8332.JPG
