Lucassifoni/hyperbolic-200mm-f3.5-/figuring/session 43/_MG_8339.JPG

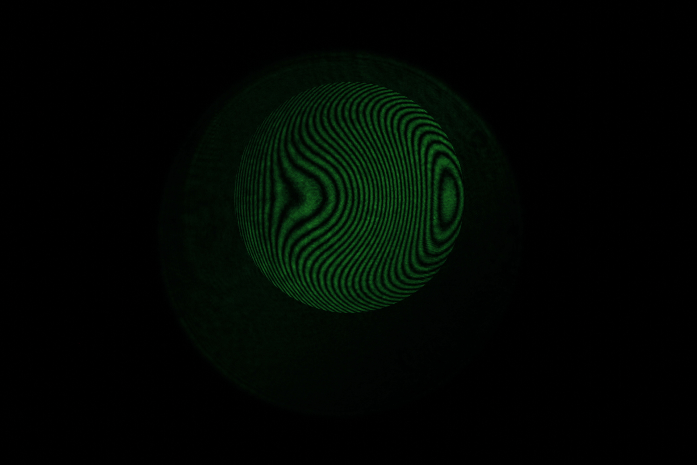
figuring/session 43/_MG_8339.JPG
