Lucassifoni/hyperbolic-200mm-f3.5-/figuring/session 44/0/_MG_8359.JPG

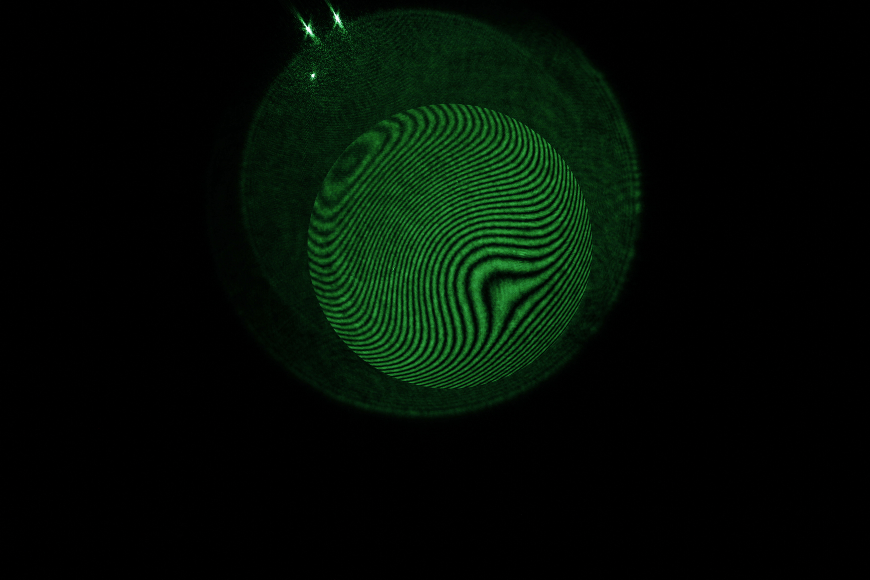
figuring/session 44/0/_MG_8359.JPG
