Lucassifoni/hyperbolic-200mm-f3.5-/figuring/session 44/45/_MG_8365.JPG

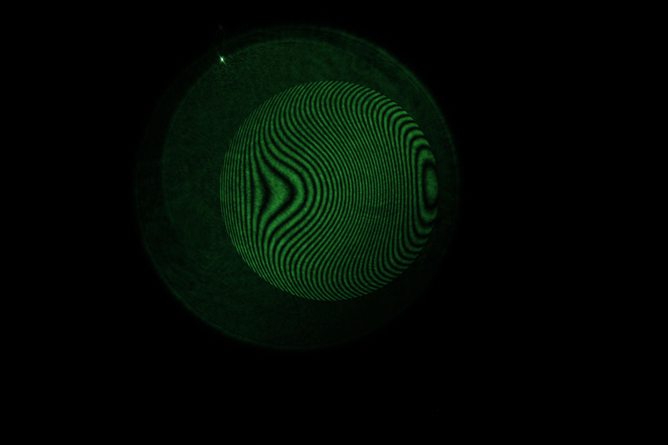
figuring/session 44/45/_MG_8365.JPG
