Lucassifoni/hyperbolic-200mm-f3.5-/figuring/session 44/90/_MG_8381.JPG

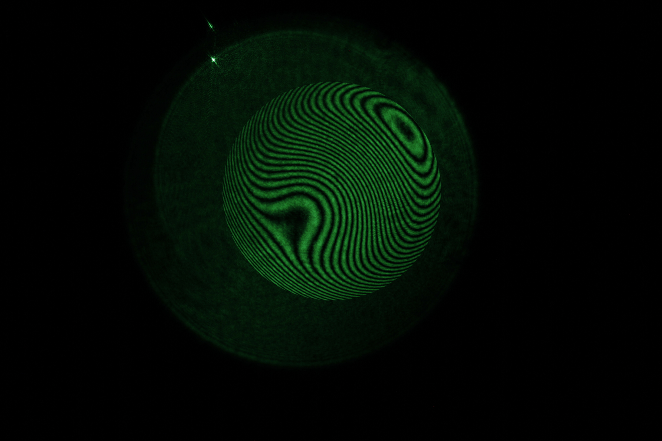
figuring/session 44/90/_MG_8381.JPG
