Lucassifoni/hyperbolic-200mm-f3.5-/figuring/session 50/_MG_8477.JPG

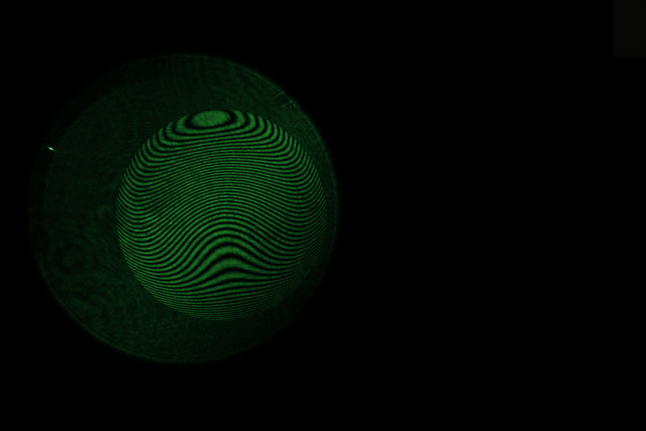
figuring/session 50/_MG_8477.JPG
