Lucassifoni/hyperbolic-200mm-f3.5-/finished/_MG_8525.JPG

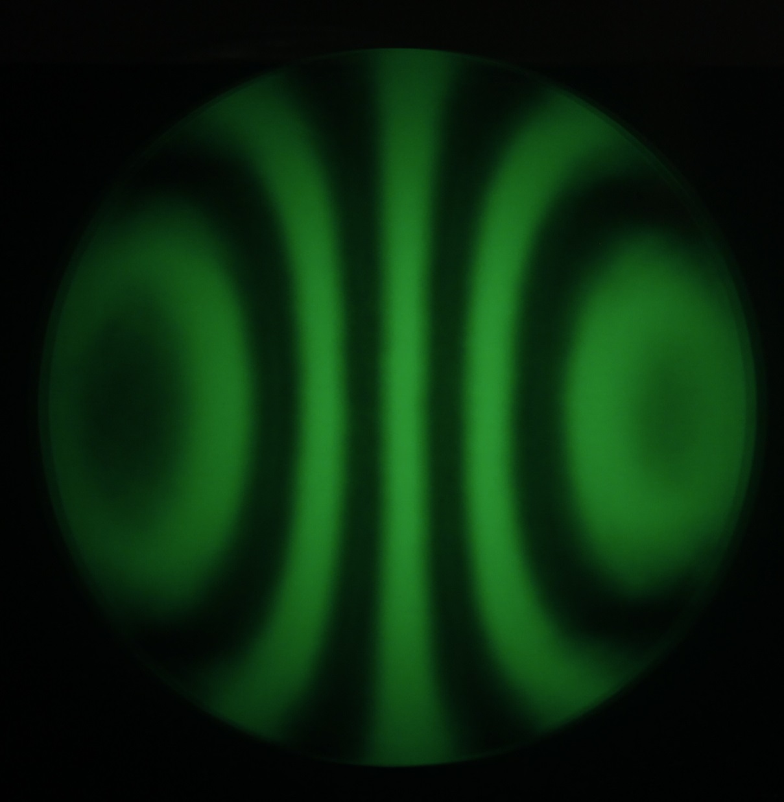
finished/_MG_8525.JPG
