Lucassifoni/hyperbolic-200mm-f3.5-/grinding/0.jpeg

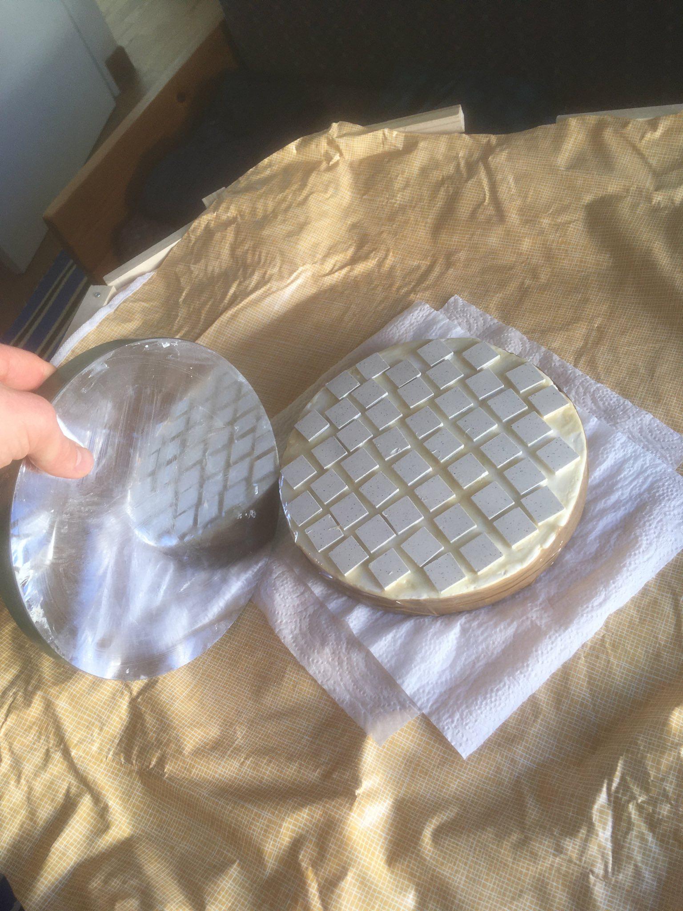
grinding/0.jpeg
