Lucassifoni/hyperbolic-200mm-f3.5-/grinding/2.jpeg

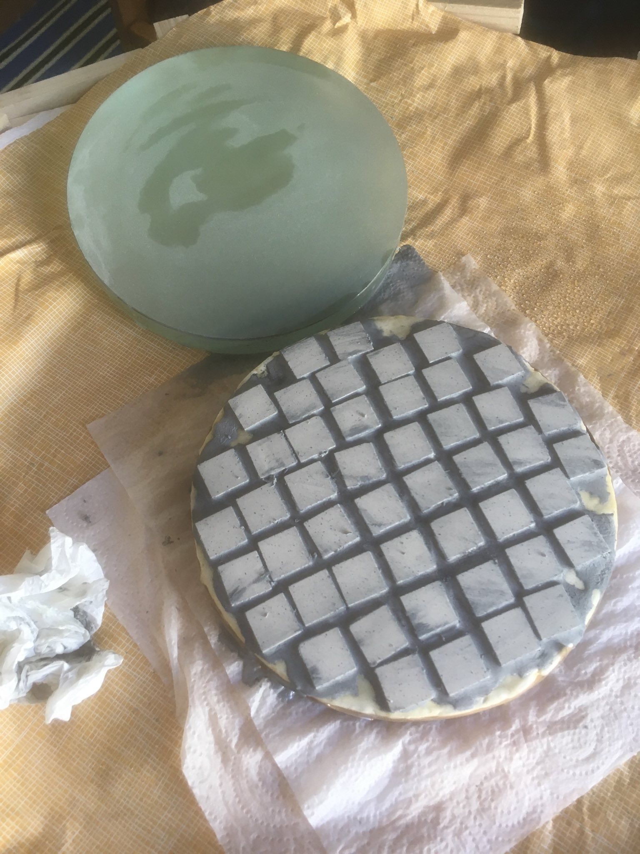
grinding/2.jpeg
