Lucassifoni/hyperbolic-200mm-f3.5-/grinding/3.jpeg

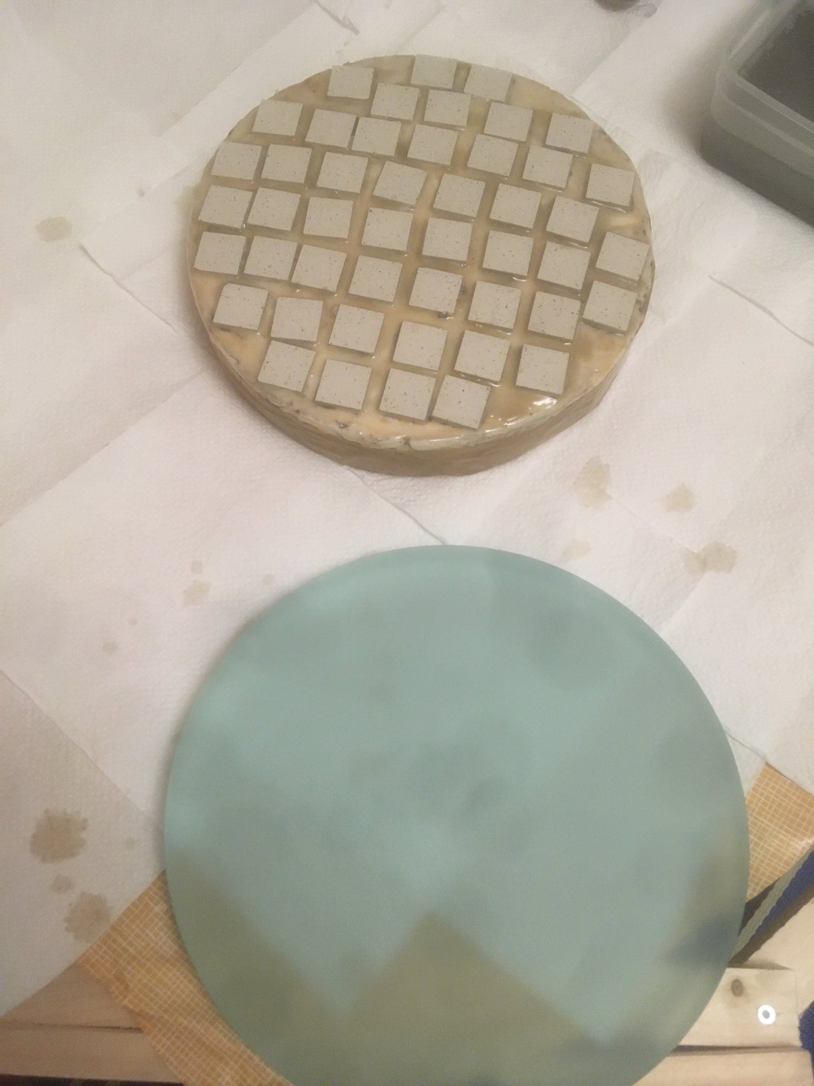
grinding/3.jpeg
