Lucassifoni/hyperbolic-200mm-f3.5-/polishing/first reflections.jpeg

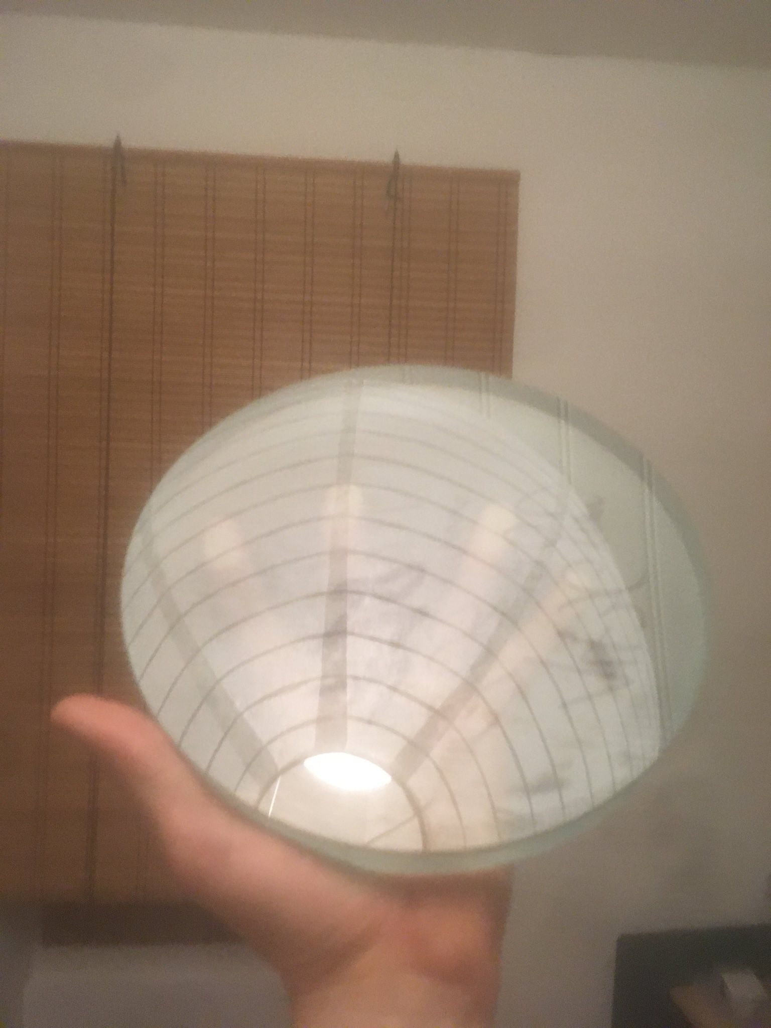
polishing/first reflections.jpeg
