Lucassifoni/hyperbolic-200mm-f3.5-/polishing/trimming lap underwater.jpeg

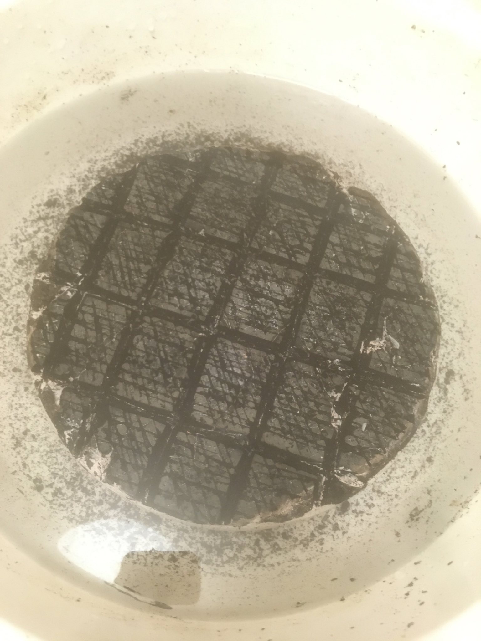
polishing/trimming lap underwater.jpeg
