Lucassifoni/hyperbolic-200mm-f3.5-/references/300fd3.7h.bmp

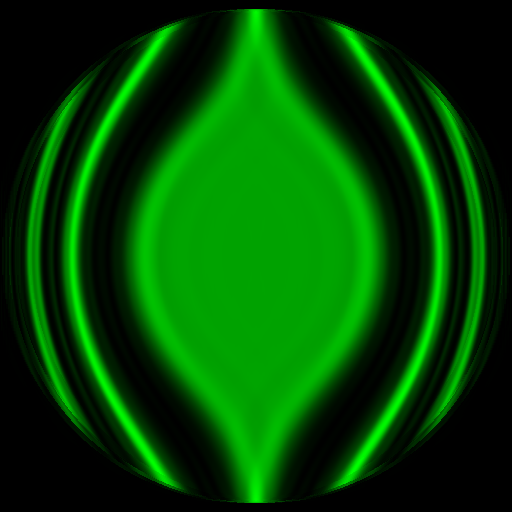
references/300fd3.7h.bmp
