Lucassifoni/hyperbolic-200mm-f3.5-/references/fd3.5i.bmp

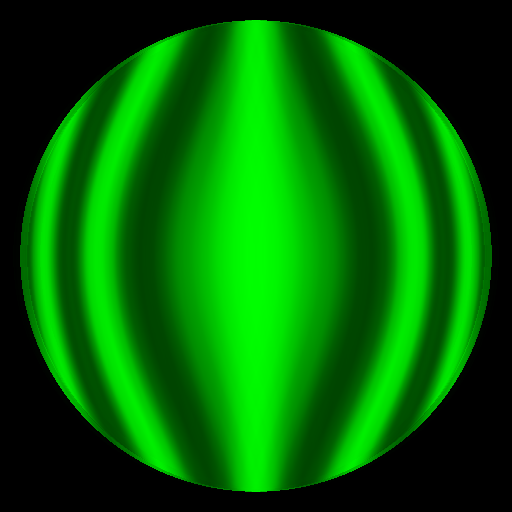
references/fd3.5i.bmp
