Lucassifoni/hyperbolic-200mm-f3.5-/references/fd6i.bmp

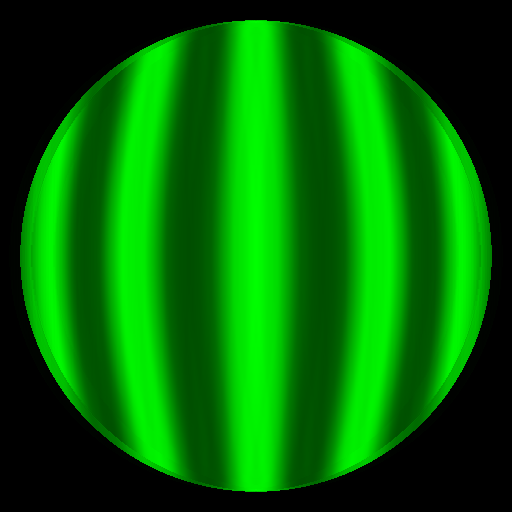
references/fd6i.bmp
