Lucassifoni/hyperbolic-200mm-f3.5-/references/fd6o.bmp

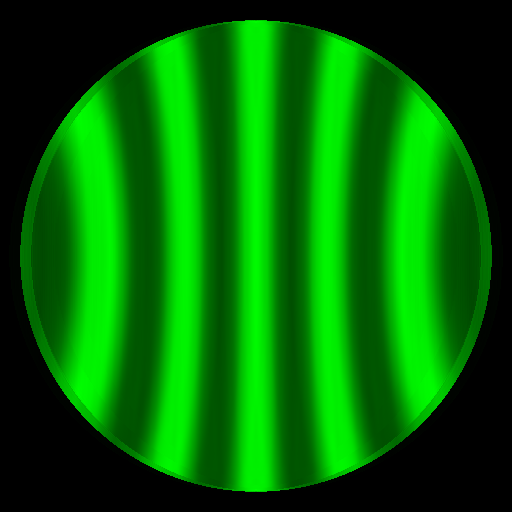
references/fd6o.bmp
