Lucassifoni/hyperbolic-200mm-f3.5-/polishing/laser test ok.jpeg

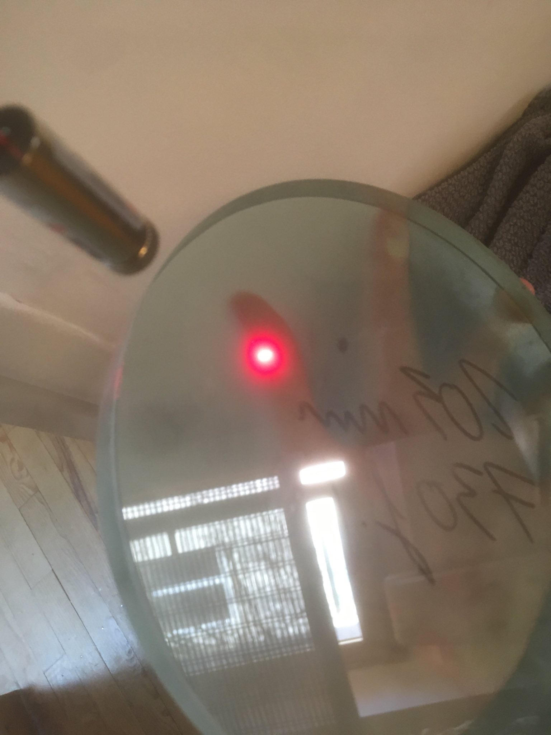
polishing/laser test ok.jpeg
